TomasPavlovicPavlo/286_schematic/MCS3201_IBM_PC_XT_AT_Floppy_Disk_Controller_1991.pdf

This Material Copyrighted By Its Respective Manufacturer
