TomasPavlovicPavlo/286_schematic/P80C287-8.pdf

This Material Copyrighted By Its Respective Manufacturer

# www.datasheet.live
