TomasPavlovicPavlo/286_schematic/HM6818.pdf

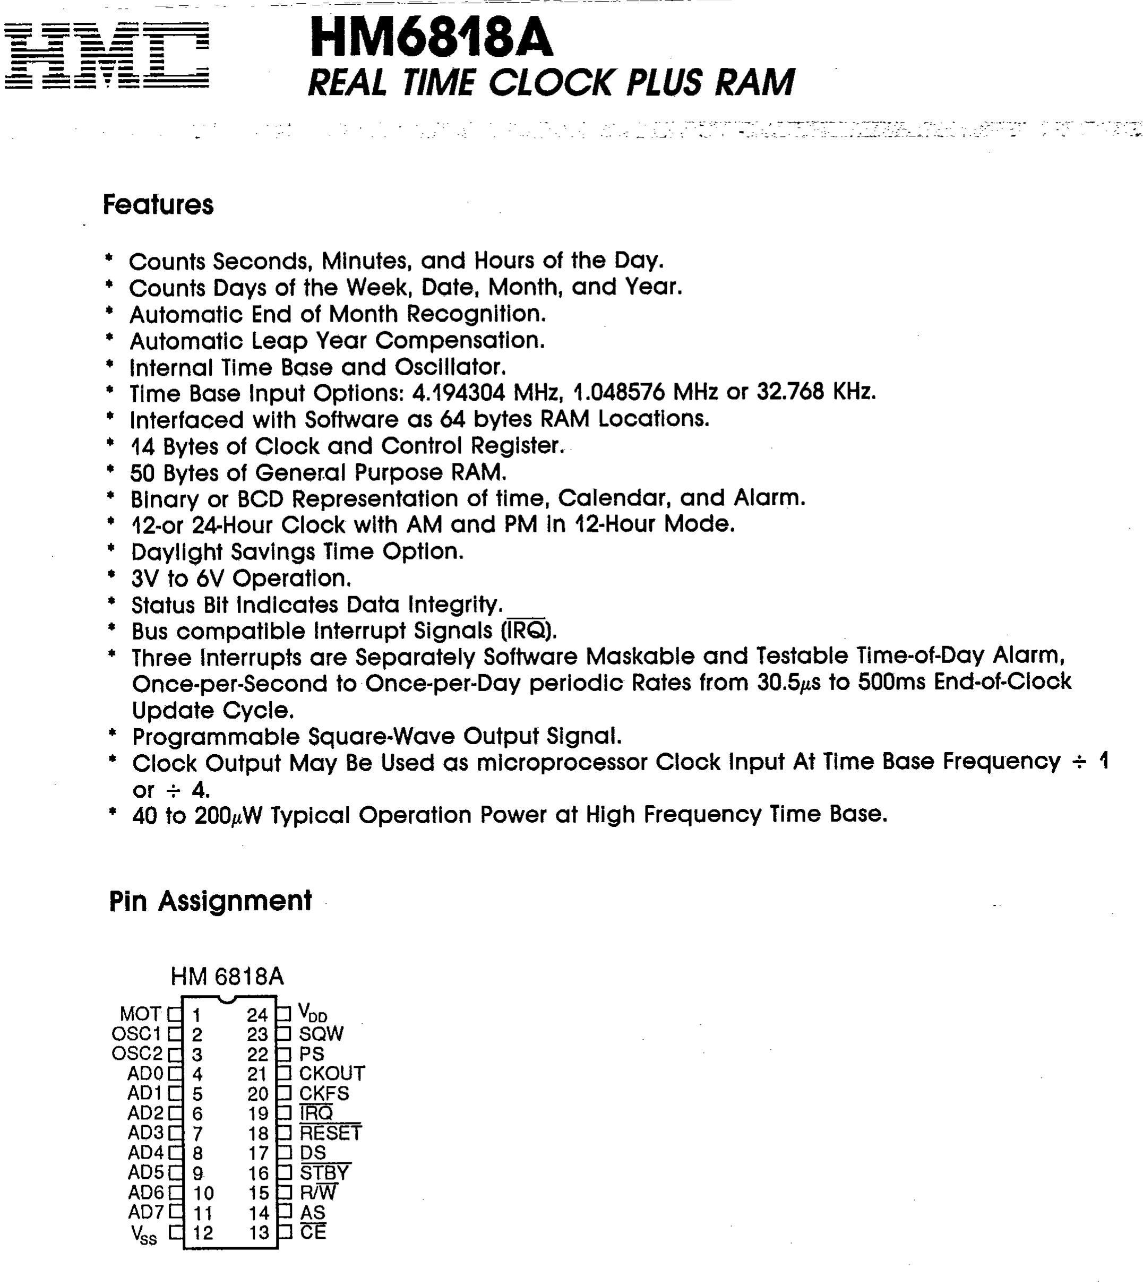
[picture p4: page 1]
