TomasPavlovicPavlo/286_schematic/IDE_controller/bot.jpg

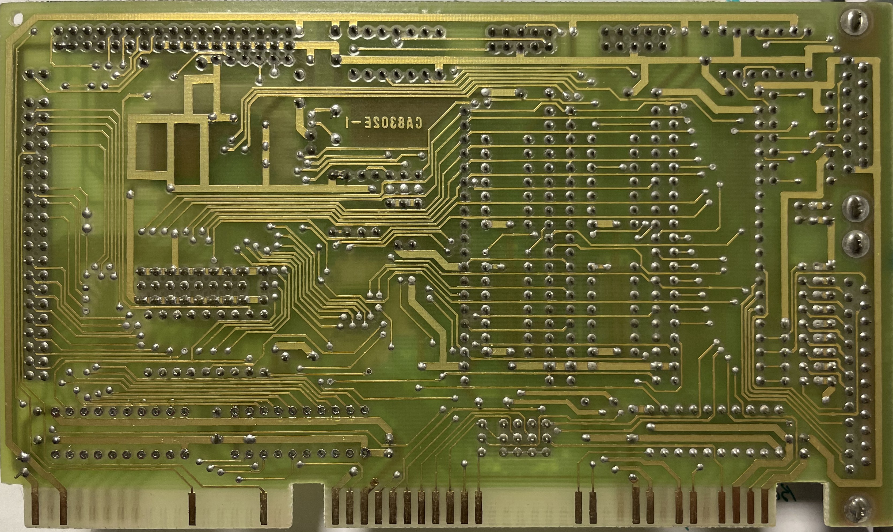
IDE_controller/bot.jpg
