TomasPavlovicPavlo/286_schematic/IDE_controller/IMG_6850.JPG

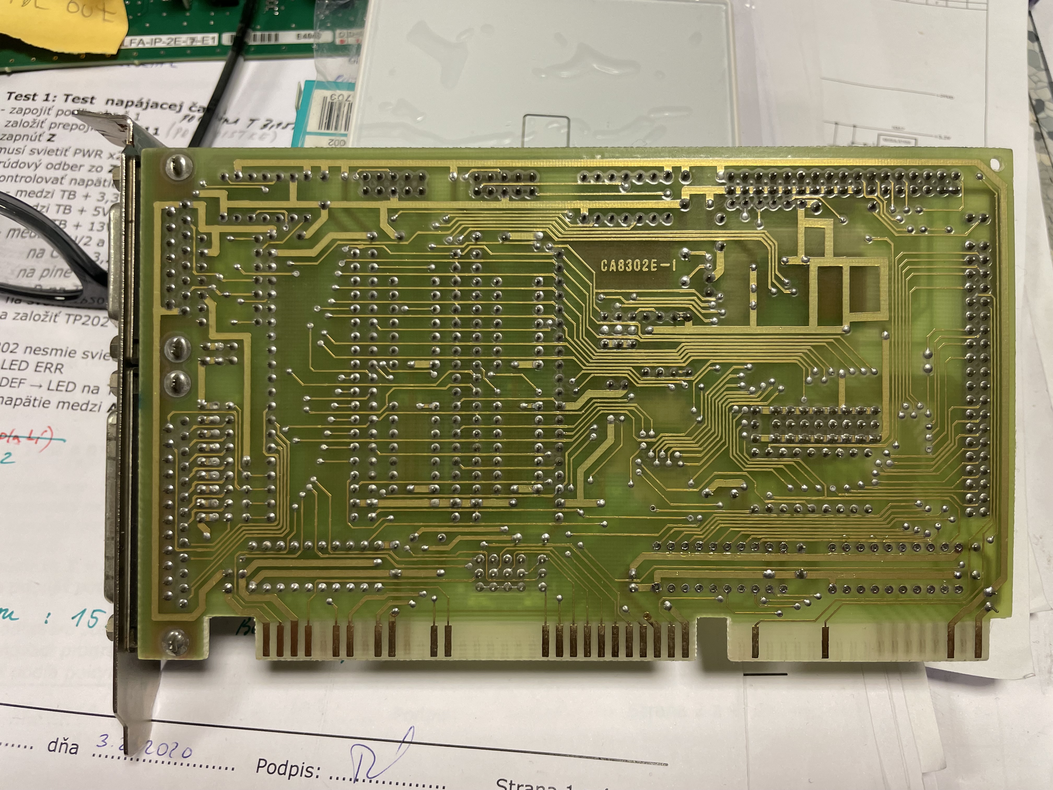
IDE_controller/IMG_6850.JPG
