TomasPavlovicPavlo/286_schematic/IDE_controller/IMG_6851.JPG

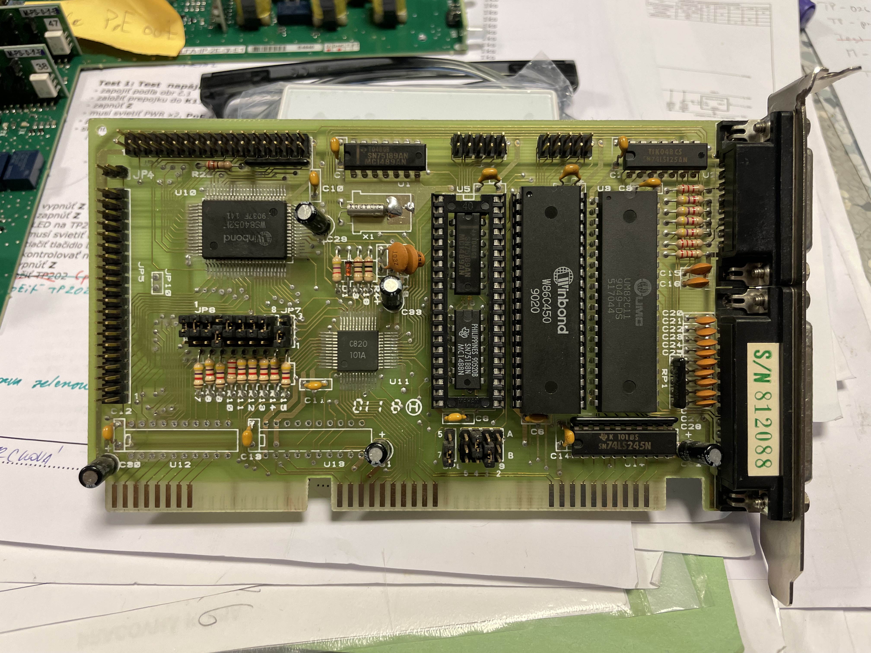
IDE_controller/IMG_6851.JPG
