TomasPavlovicPavlo/286_schematic/IDE_controller/top2.jpg

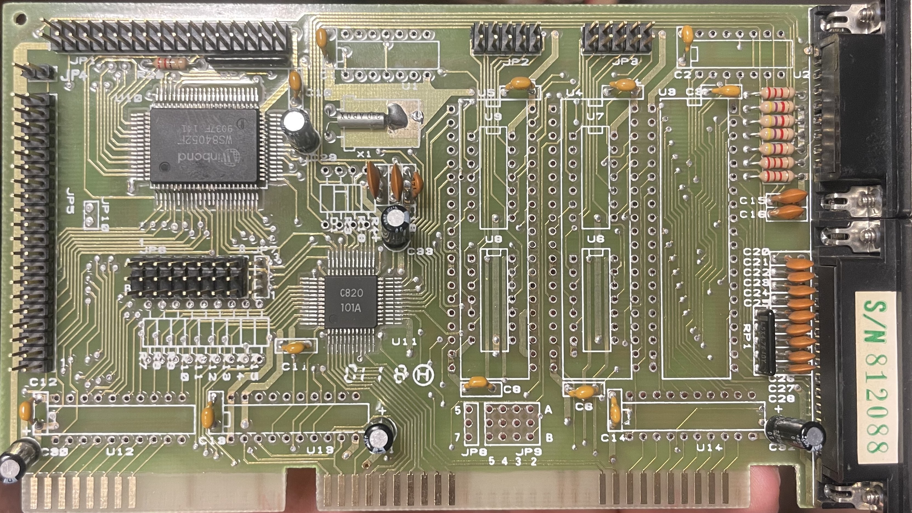
IDE_controller/top2.jpg
