TomasPavlovicPavlo/286_schematic/IDE_controller/top.jpg

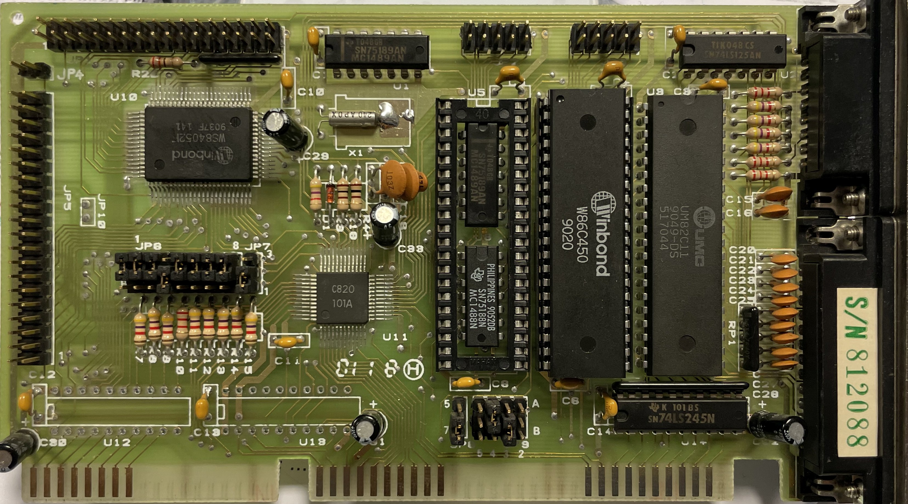
IDE_controller/top.jpg
