TomasPavlovicPavlo/286_schematic/KiCAD/suntac-286p-back-6633c3940dea2172361565.jpg

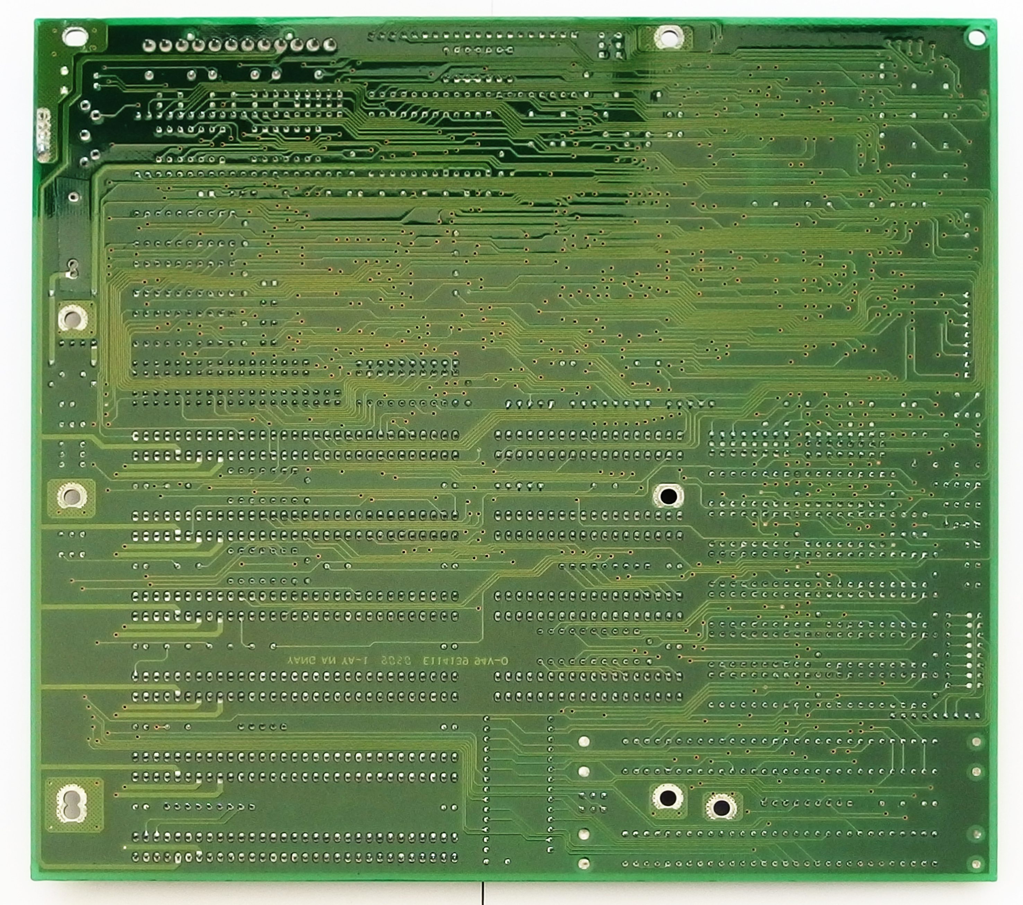
KiCAD/suntac-286p-back-6633c3940dea2172361565.jpg
