TomasPavlovicPavlo/286_schematic/KiCAD/top1.jpg

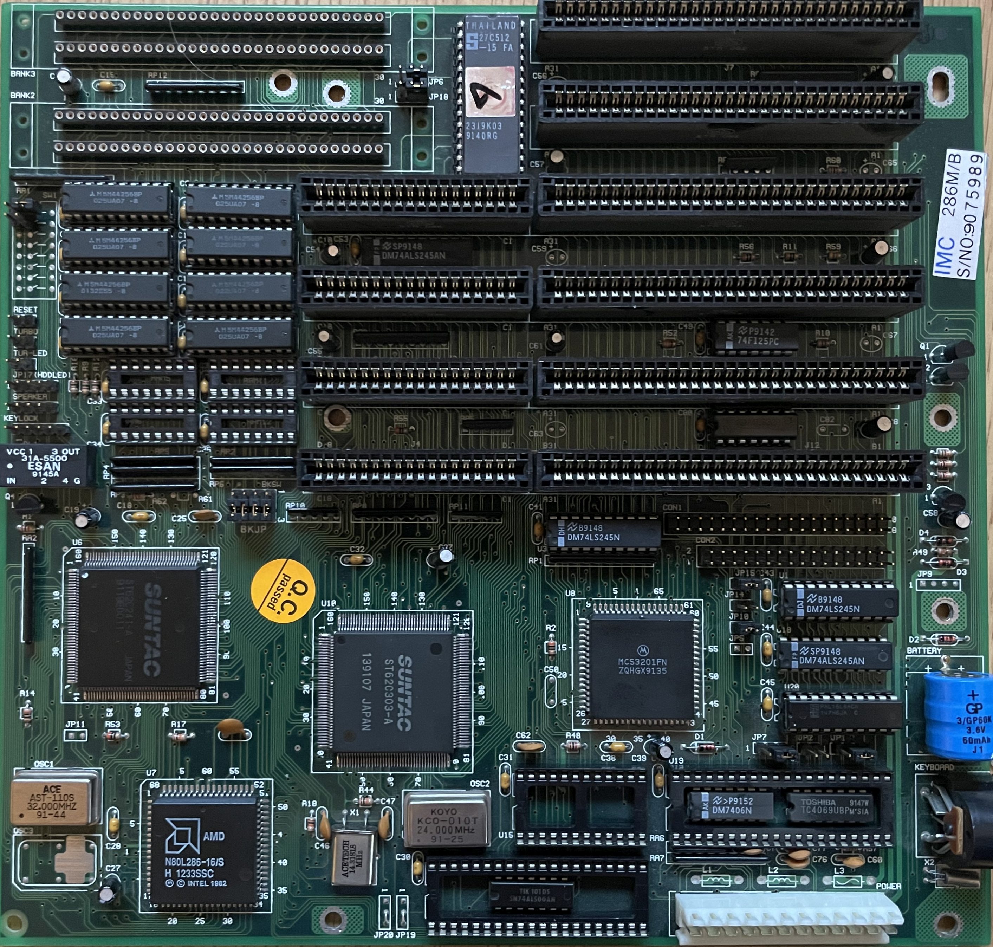
KiCAD/top1.jpg
