TomasPavlovicPavlo/286_schematic/KiCAD/top4.jpg

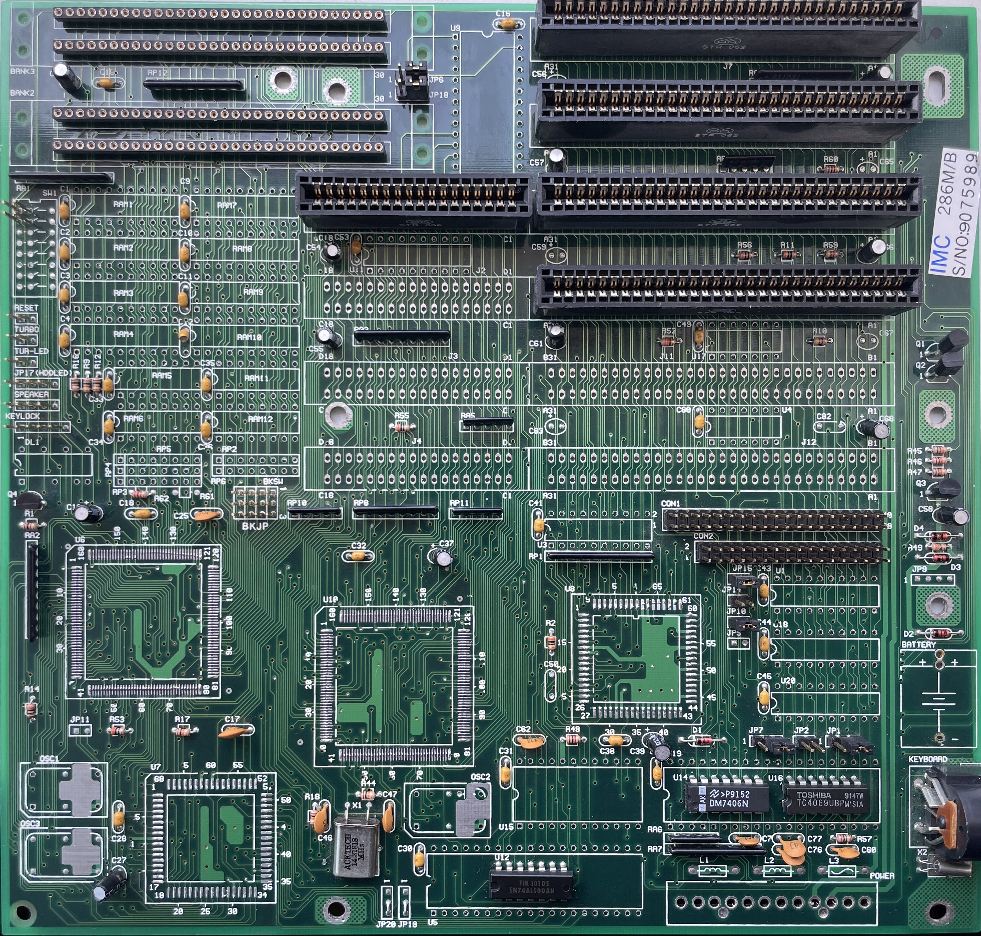
KiCAD/top4.jpg
