TomasPavlovicPavlo/286_schematic/KiCAD/top.jpg

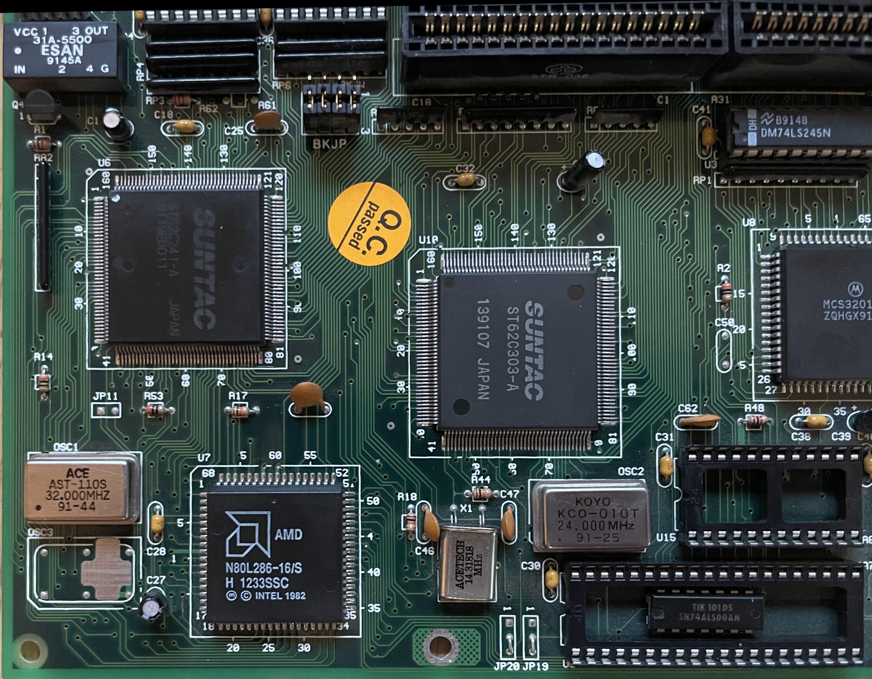
KiCAD/top.jpg
