TomasPavlovicPavlo/286_schematic/KiCAD/CPU_ChipSet1.kicad_sch

## KiCad design KiCAD/CPU_ChipSet1.kicad_sch (2025-07-21)

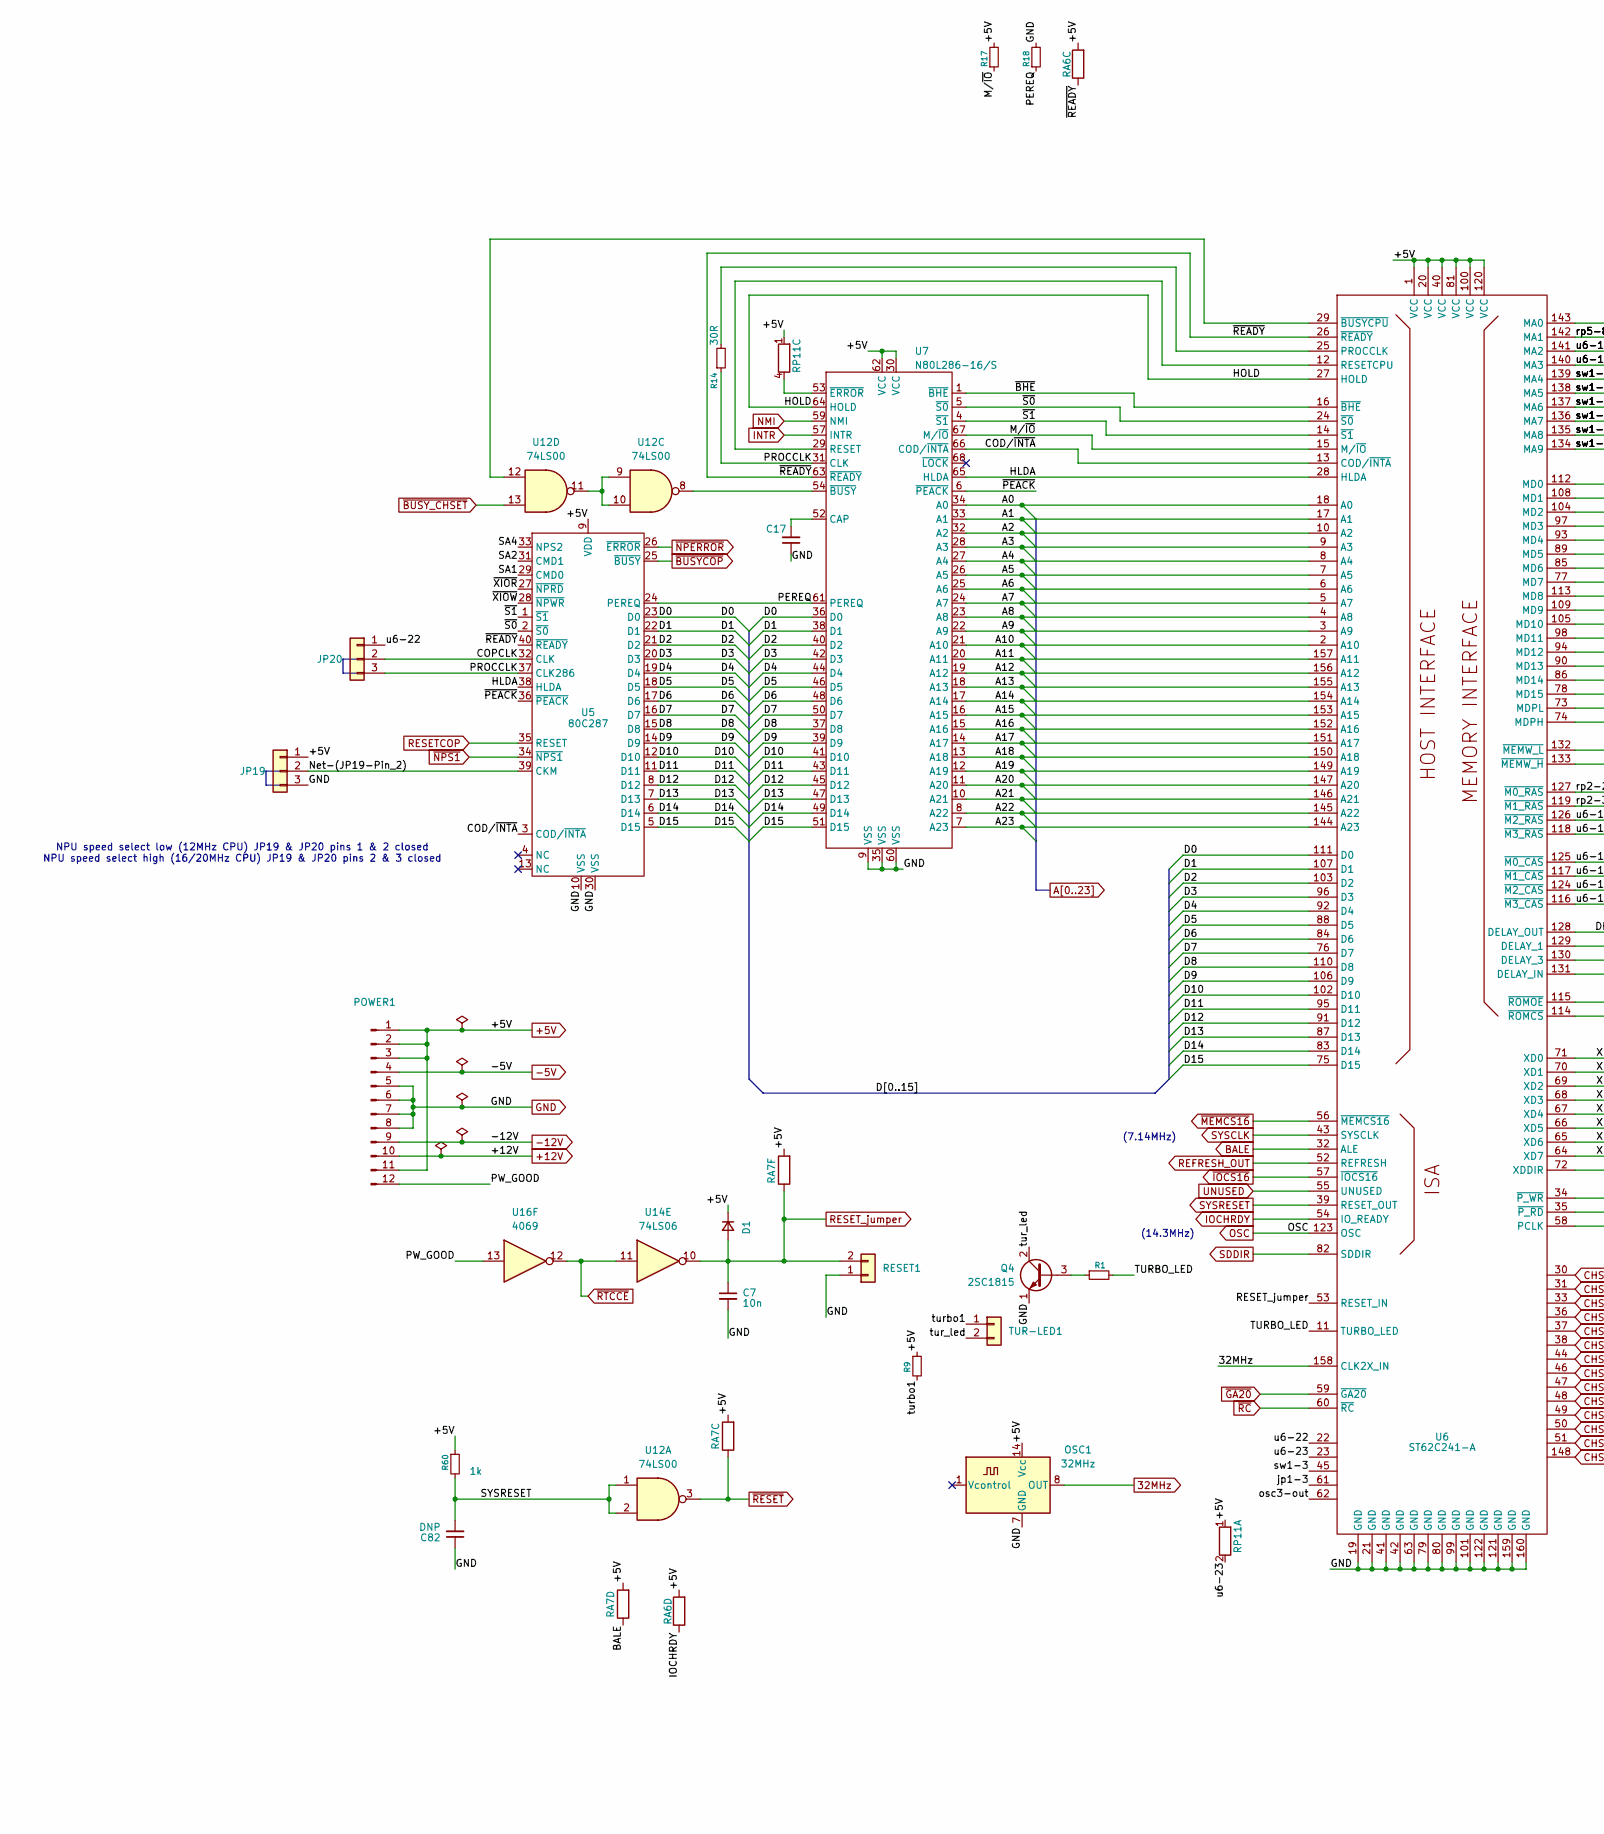
[picture p27: schematic CPU_ChipSet1.kicad_sch, part in row 1, column 1]

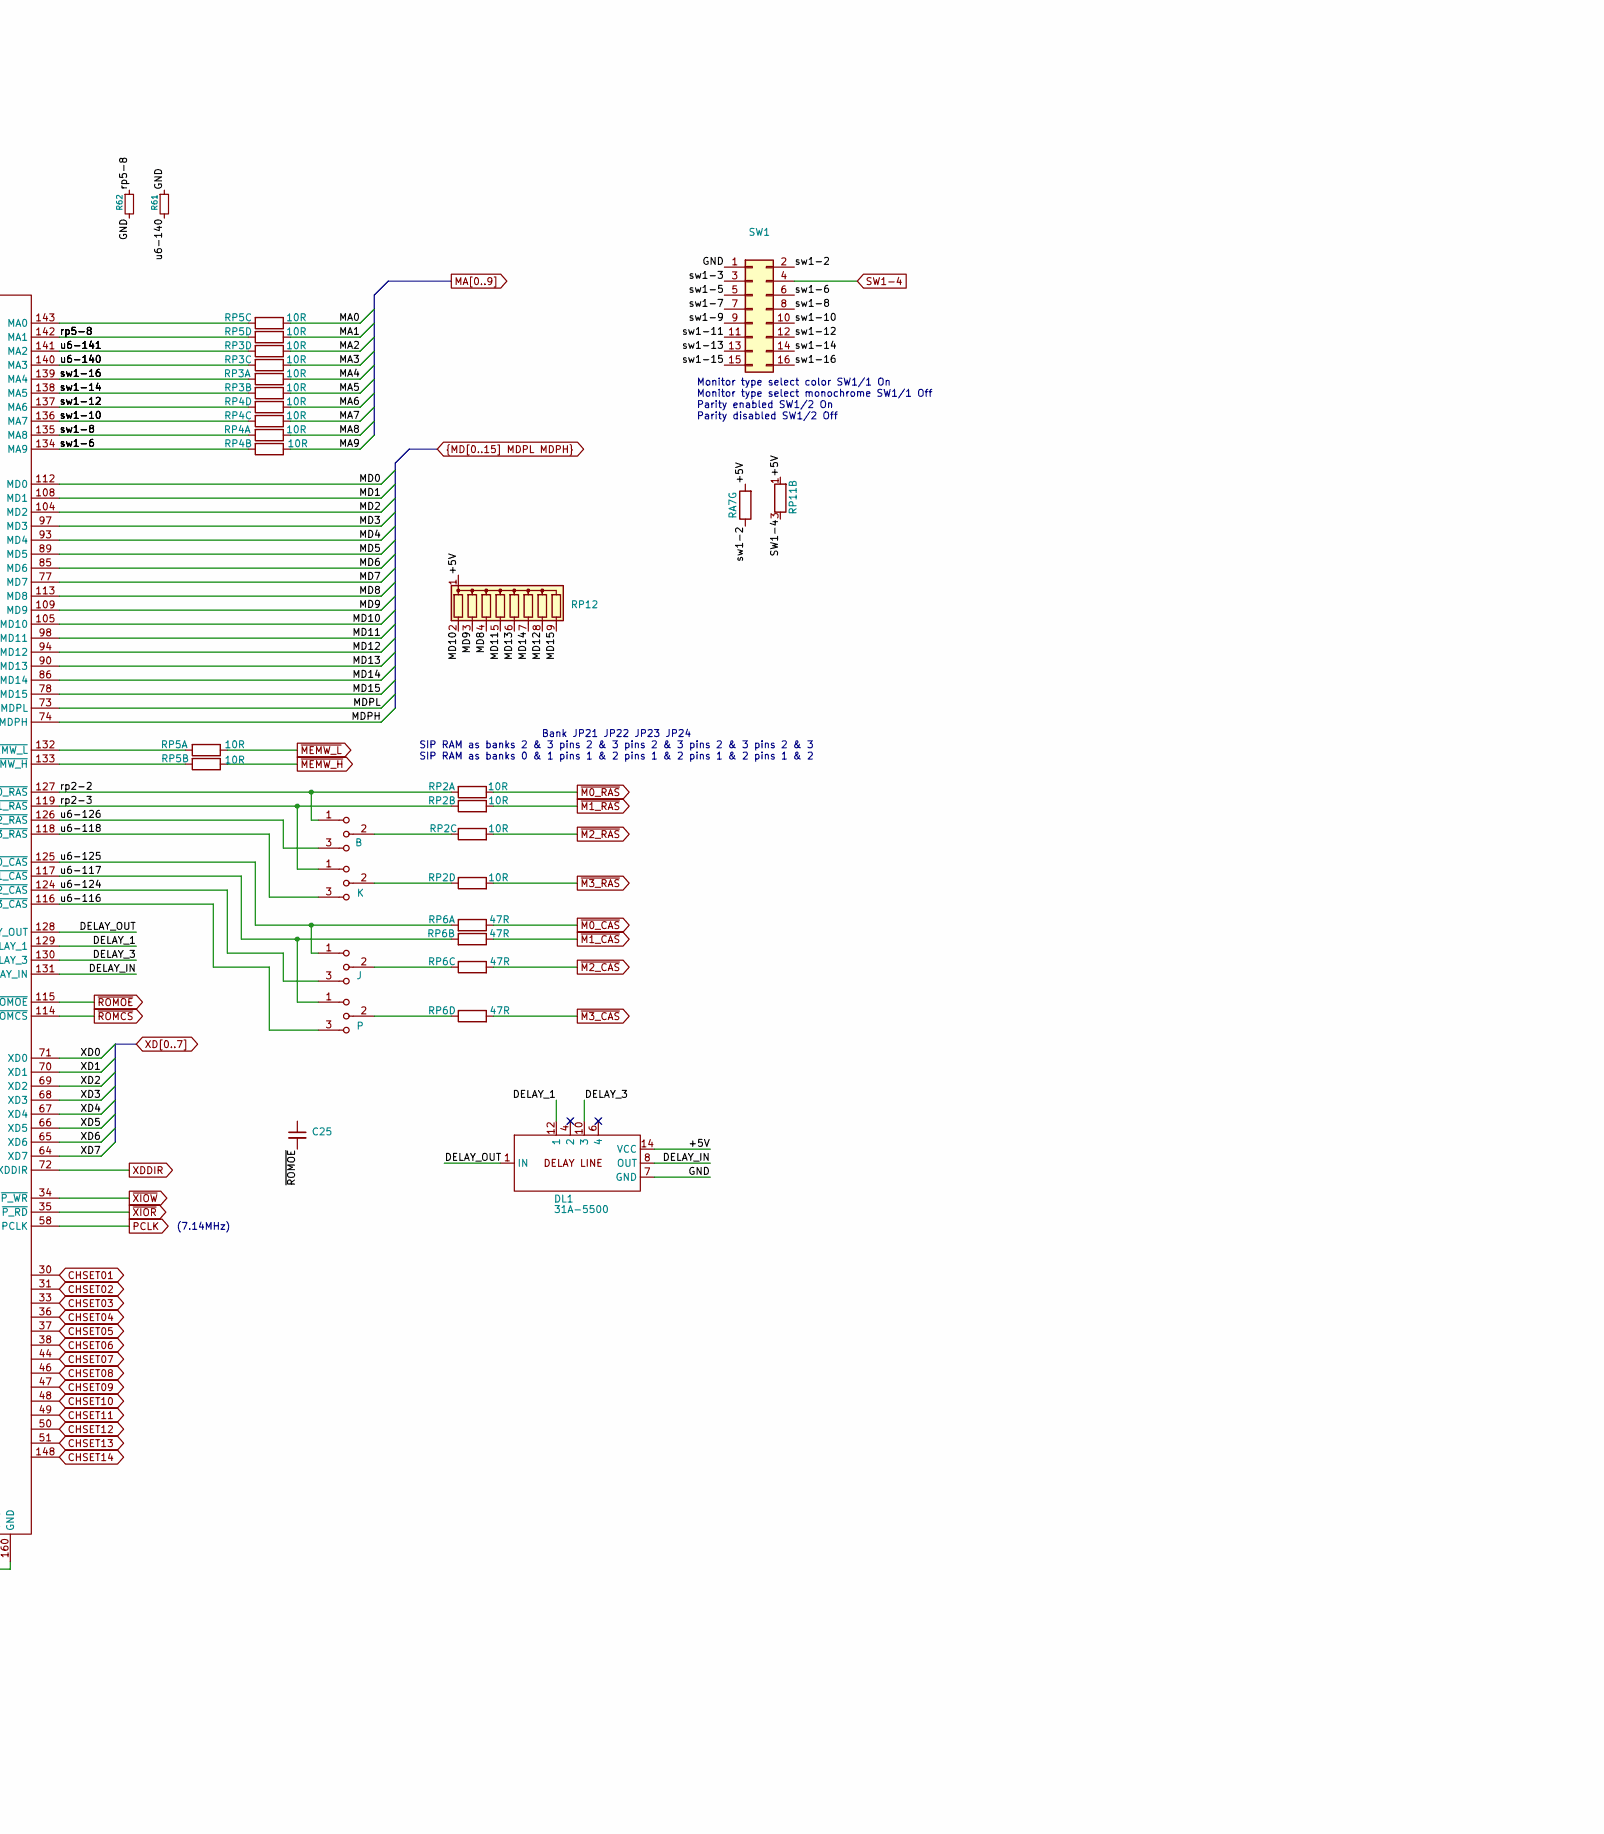
[picture p28: schematic CPU_ChipSet1.kicad_sch, part in row 1, column 2]

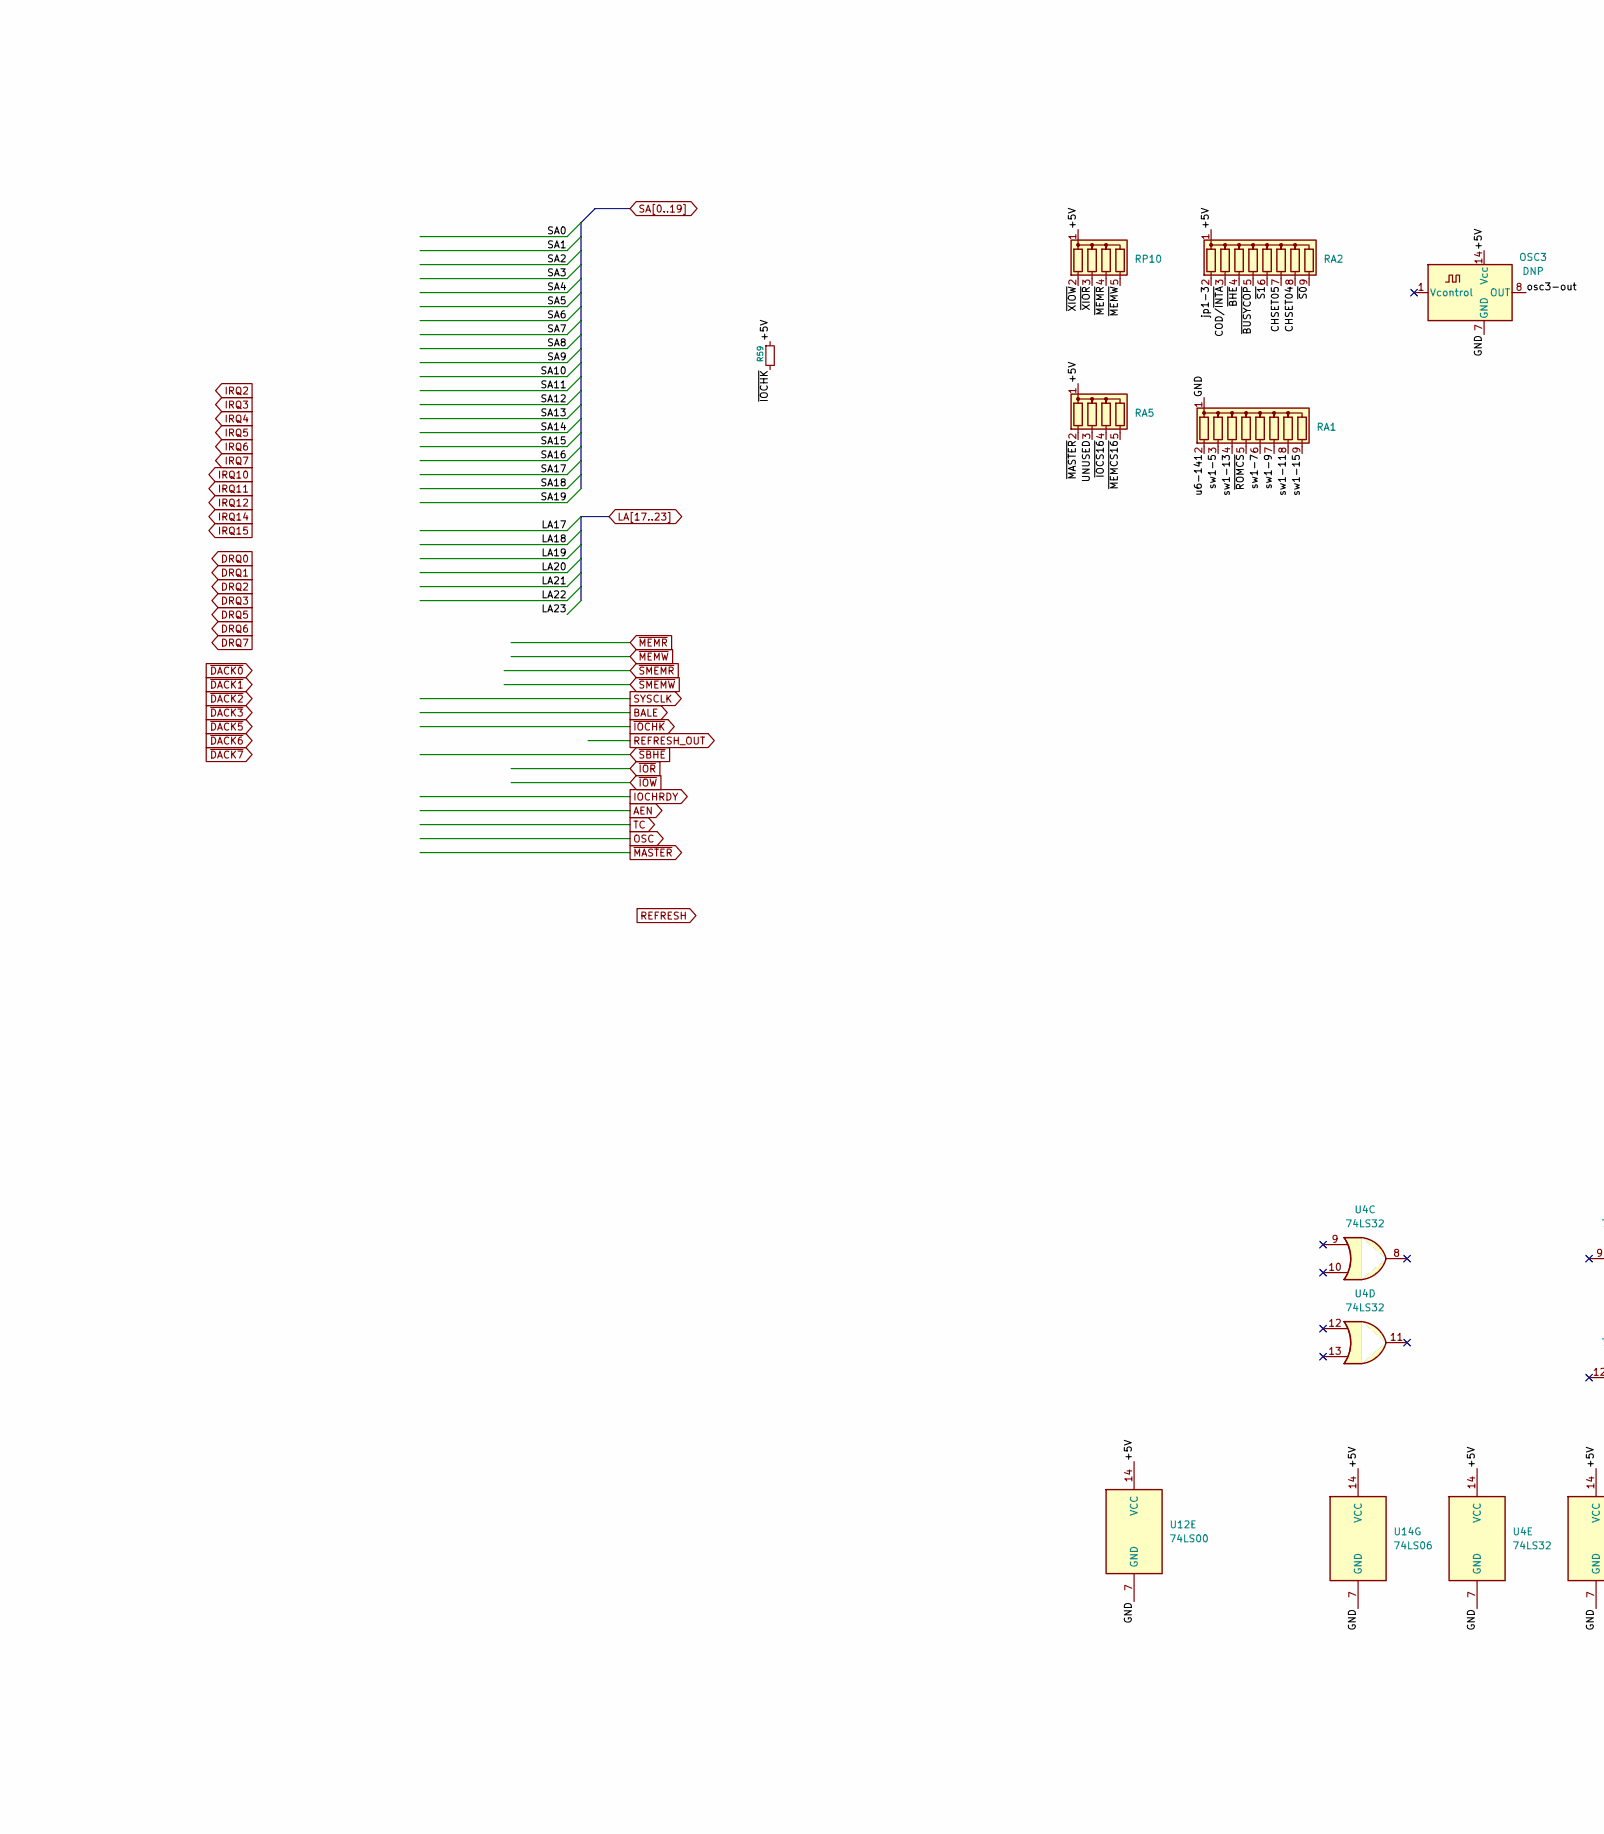
[picture p29: schematic CPU_ChipSet1.kicad_sch, part in row 2, column 1]

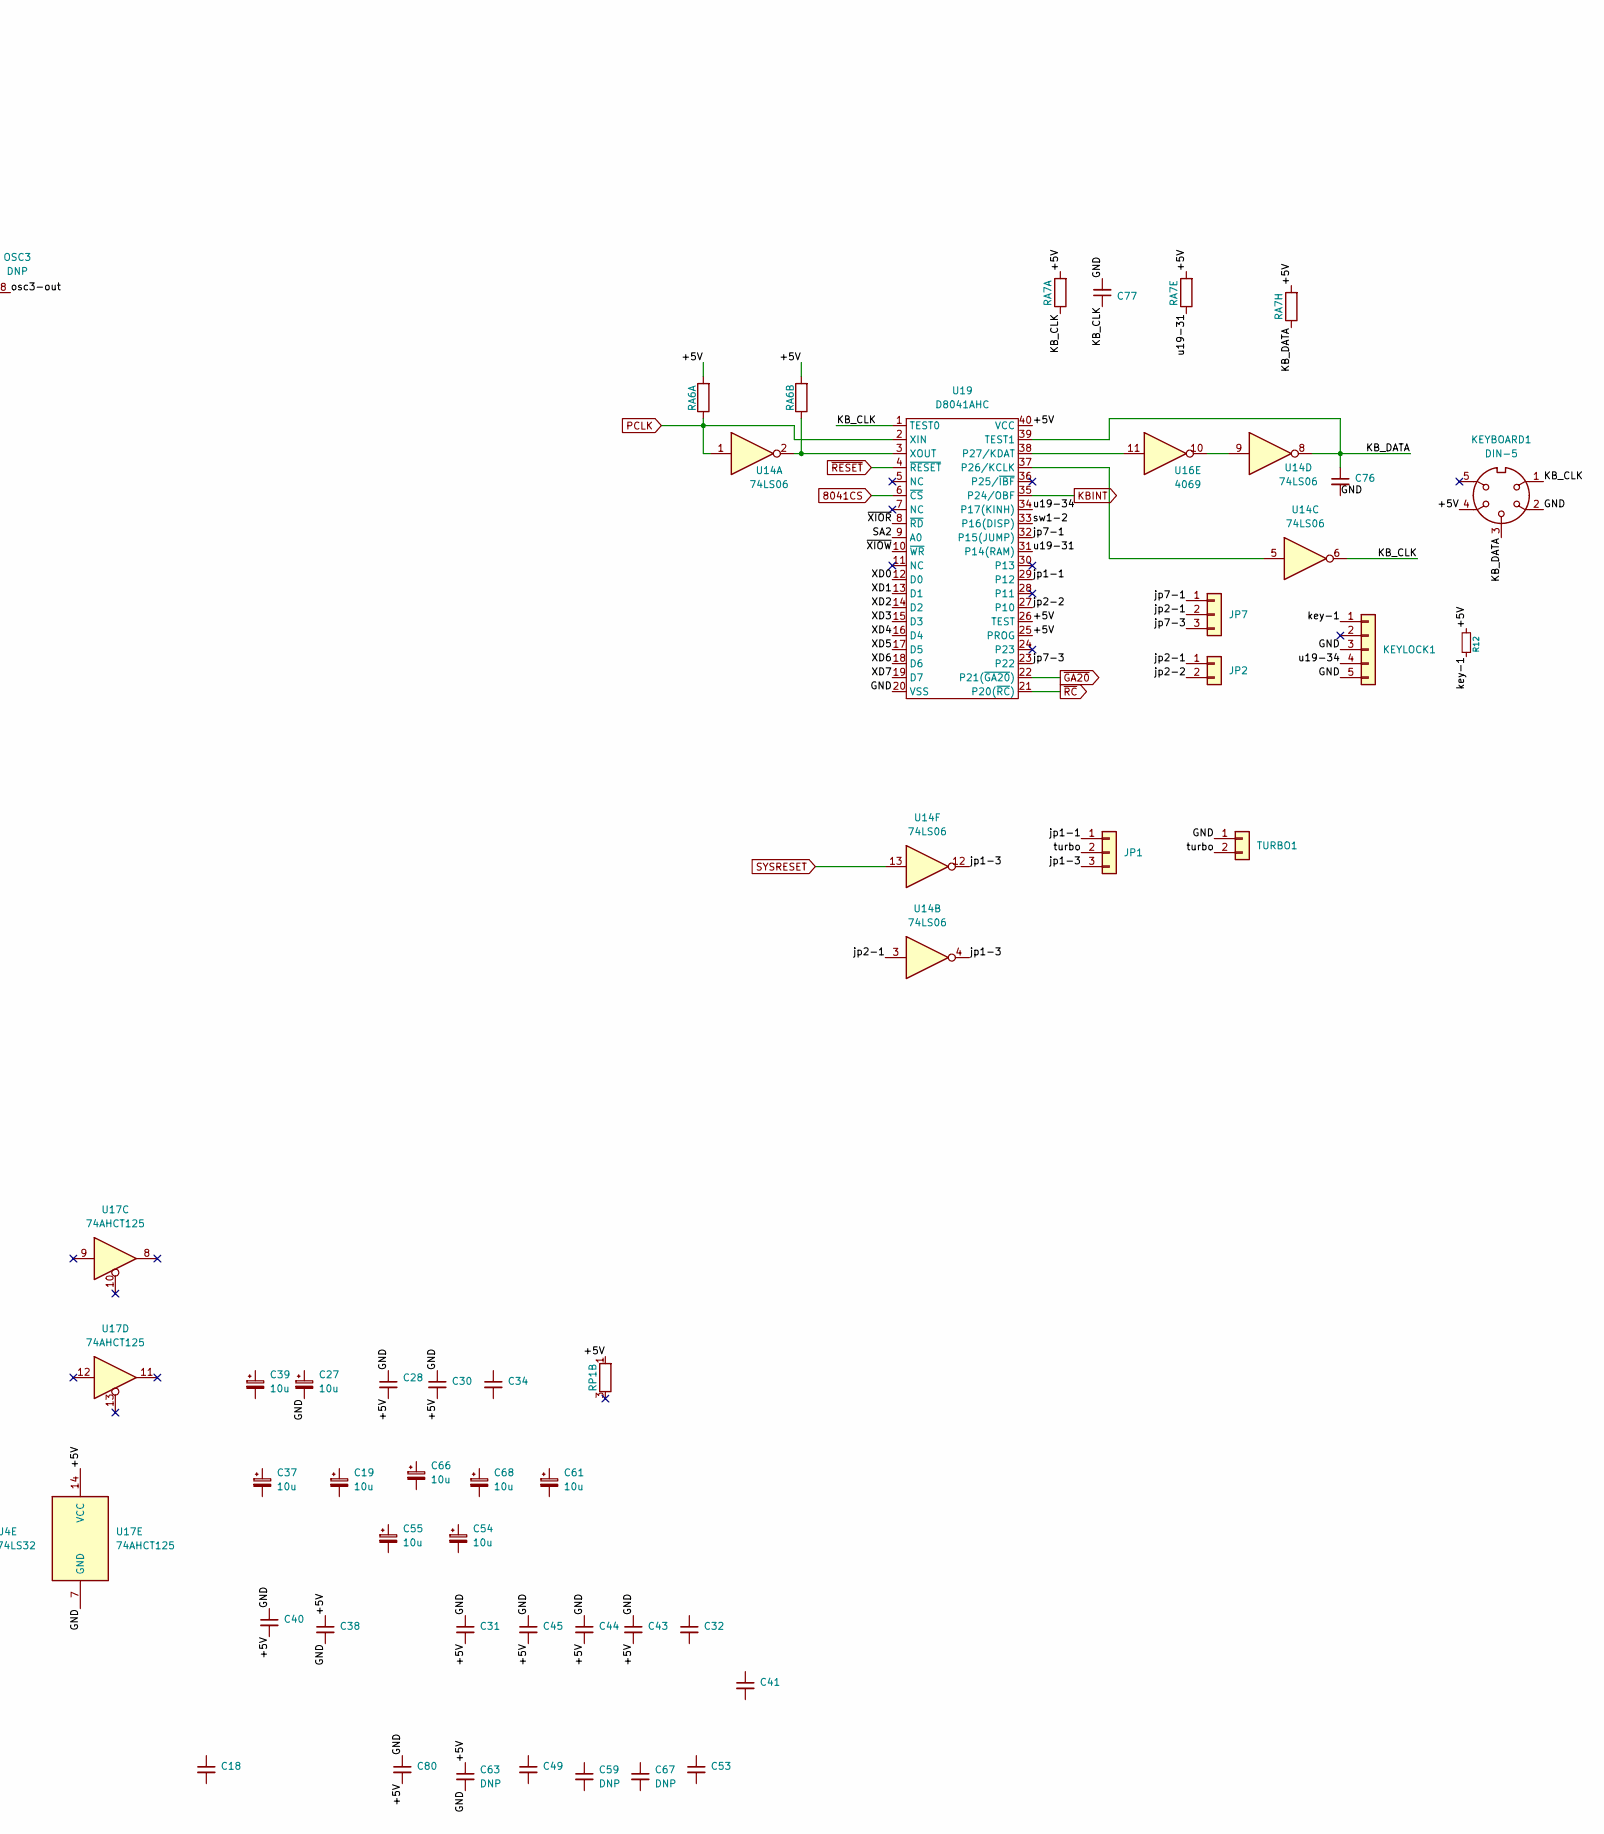
[picture p30: schematic CPU_ChipSet1.kicad_sch, part in row 2, column 2]

Parts:
BKSW1: B; PinHeader_1x03_P2.54mm_Vertical
BKSW2: K; PinHeader_1x03_P2.54mm_Vertical
BKSW3: J; PinHeader_1x03_P2.54mm_Vertical
BKSW4: P; PinHeader_1x03_P2.54mm_Vertical
C7: 10n; C_Disc_D4.3mm_W1.9mm_P5.00mm
C17, C18, C25, C28, C30, C31, C32, C34, C38, C40, C41, C43, C44, C45, C49, C53, C76, C77, C80: C_Disc_D4.3mm_W1.9mm_P5.00mm
C19, C27, C37, C39, C54, C55, C61, C66, C68: 10u; CP_Radial_D5.0mm_P2.50mm
C59, C63, C67: DNP; C_Disc_D3.0mm_W1.6mm_P2.50mm
C82: DNP; C_Disc_D4.3mm_W1.9mm_P5.00mm
D1: D_Small; D_A-405_P10.16mm_Horizontal
DL1: 31A-5500
JP1, JP7, JP19, JP20: Conn_01x03; PinHeader_1x03_P2.54mm_Vertical
JP2: Conn_01x02; PinSocket_1x02_P2.54mm_Vertical
KEYBOARD1: DIN-5; 286_DIN5
KEYLOCK1: Conn_01x05; PinHeader_1x05_P2.54mm_Vertical
OSC1: 32MHz; Oscillator_DIP-14
OSC3: DNP; Oscillator_DIP-14
POWER1: Conn_01x12_Pin; Molex_KK-396_A-41791-0012_1x12_P3.96mm_Vertical
Q4: 2SC1815; TO-92L_Inline_Wide
R1, R17, R18, R59, R61, R62: R_Small; R_Axial_DIN0204_L3.6mm_D1.6mm_P5.08mm_Horizontal
R9, R12: R_Small; R_Axial_L3.6mm_D1.6mm_P4.5mm_Horizontal
R14: 30R; R_Axial_DIN0204_L3.6mm_D1.6mm_P5.08mm_Horizontal
R60: 1k; R_Axial_L3.6mm_D1.6mm_P4.5mm_Horizontal
RA1, RA2, RA7: R_Network08; R_Array_SIP9
RA5, RA6: R_Network04; R_Array_SIP5
RESET1: Conn_01x02; PinSocket_1x02_P2.54mm_Vertical
RP1: R_Network09; R_Array_SIP10
RP2, RP3, RP4, RP5: 10R; R_Array_SIP8
RP6: 47R; R_Array_SIP8
RP10, RP11: R_Network04; R_Array_SIP5
RP12: R_Network08; R_Array_SIP9
SW1: Conn_02x08_Odd_Even; PinHeader_2x08_P2.54mm_Vertical
TUR-LED1: Conn_01x02; PinSocket_1x02_P2.54mm_Vertical
TURBO1: Conn_01x02; PinSocket_1x02_P2.54mm_Vertical
U4: 74LS32; DIP-14_W7.62mm
U5: 80C287; DIP-40_W15.24mm_Socket_small_pad
U6: ST62C241-A; PQFP-160_28x28mm_P0.65mm
U7: N80L286-16/S; PLCC-68_from_1
U12: 74LS00; DIP-14_W7.62mm
U14: 74LS06; DIP-14_W7.62mm
U16: 4069; DIP-14_W7.62mm
U17: 74AHCT125; DIP-14_W7.62mm
U19: D8041AHC; DIP-40_W15.24mm_Socket_small_pad

Connections:
32MHz: OSC1.8 (OUT), U6.158 (CLK2X_IN)
8041CS: U19.6 (~CS)
+5V: C28.2, C30.2, C31.2, C38.1, C40.2, C43.2, C44.2, C45.2, C63.1, C80.2, D1.1 (K), DL1.14 (VCC), JP19.1, KEYBOARD1.4, OSC1.14 (Vcc), OSC3.14 (Vcc), POWER1.1, POWER1.2, POWER1.3, POWER1.11, R9.1, R12.2, R17.2, R59.1, R60.1, RA2.1 (common), RA5.1 (common), RA6.1 (R1), RA7.1 (R1), RP1.1 (R1), RP10.1 (common), RP11.1 (R1), RP12.1 (common), U4.14 (VCC), U5.9 (VDD), U6.1 (VCC), U6.20 (VCC), U6.40 (VCC), U6.81 (VCC), U6.100 (VCC), U6.120 (VCC), U7.30 (VCC), U7.62 (VCC), U12.14 (VCC), U14.14 (VCC), U17.14 (VCC), U19.25 (PROG), U19.26 (TEST), U19.40 (VCC)
+12V: POWER1.10
-5V: POWER1.4
-12V: POWER1.9
A0: U6.18 (A0), U7.34 (A0)
A1: U6.17 (A1), U7.33 (A1)
A2: U6.10 (A2), U7.32 (A2)
A3: U6.9 (A3), U7.28 (A3)
A4: U6.8 (A4), U7.27 (A4)
A5: U6.7 (A5), U7.26 (A5)
A6: U6.6 (A6), U7.25 (A6)
A7: U6.5 (A7), U7.24 (A7)
A8: U6.4 (A8), U7.23 (A8)
A9: U6.3 (A9), U7.22 (A9)
A10: U6.2 (A10), U7.21 (A10)
A11: U6.157 (A11), U7.20 (A11)
A12: U6.156 (A12), U7.19 (A12)
A13: U6.155 (A13), U7.18 (A13)
A14: U6.154 (A14), U7.17 (A14)
A15: U6.153 (A15), U7.16 (A15)
A16: U6.152 (A16), U7.15 (A16)
A17: U6.151 (A17), U7.14 (A17)
A18: U6.150 (A18), U7.13 (A18)
A19: U6.149 (A19), U7.12 (A19)
A20: U6.147 (A20), U7.11 (A20)
A21: U6.146 (A21), U7.10 (A21)
A22: U6.145 (A22), U7.8 (A22)
A23: U6.144 (A23), U7.7 (A23)
BALE: RA7.5 (R4.2), U6.32 (ALE)
CHSET01: U6.30
CHSET02: U6.31
CHSET03: U6.33
CHSET04: RA2.8 (R7), U6.36
CHSET05: RA2.7 (R6), U6.37
CHSET06: U6.38
CHSET07: U6.44
CHSET08: U6.46
CHSET09: U6.47
CHSET10: U6.48
CHSET11: U6.49
CHSET12: U6.50
CHSET13: U6.51
CHSET14: U6.148
COD/~INTA: RA2.3 (R2), U5.3 (COD/~INTA), U6.13 (COD/~INTA), U7.66 (COD/~INTA)
COPCLK: JP20.2, U5.32 (CLK)
D0: U5.23 (D0), U6.111 (D0), U7.36 (D0)
D1: U5.22 (D1), U6.107 (D1), U7.38 (D1)
D2: U5.21 (D2), U6.103 (D2), U7.40 (D2)
D3: U5.20 (D3), U6.96 (D3), U7.42 (D3)
D4: U5.19 (D4), U6.92 (D4), U7.44 (D4)
D5: U5.18 (D5), U6.88 (D5), U7.46 (D5)
D6: U5.17 (D6), U6.84 (D6), U7.48 (D6)
D7: U5.16 (D7), U6.76 (D7), U7.50 (D7)
D8: U5.15 (D8), U6.110 (D8), U7.37 (D8)
D9: U5.14 (D9), U6.106 (D9), U7.39 (D9)
D10: U5.12 (D10), U6.102 (D10), U7.41 (D10)
D11: U5.11 (D11), U6.95 (D11), U7.43 (D11)
D12: U5.8 (D12), U6.91 (D12), U7.45 (D12)
D13: U5.7 (D13), U6.87 (D13), U7.47 (D13)
D14: U5.6 (D14), U6.83 (D14), U7.49 (D14)
D15: U5.5 (D15), U6.75 (D15), U7.3 (NC), U7.51 (D15), U7.56 (NC)
DELAY_1: DL1.12 (1), U6.129 (DELAY_1)
DELAY_3: DL1.10 (3), U6.130 (DELAY_3)
DELAY_IN: DL1.8 (OUT), U6.131 (DELAY_IN)
DELAY_OUT: DL1.1 (IN), U6.128 (DELAY_OUT)
GND: C7.2, C17.1, C27.2, C28.1, C30.1, C31.1, C38.2, C40.1, C43.1, C44.1, C45.1, C63.2, C76.2, C77.2, C80.1, C82.1, DL1.7 (GND), JP19.3, KEYBOARD1.2, KEYLOCK1.3, KEYLOCK1.5, OSC1.7 (GND), OSC3.7 (GND), POWER1.5, POWER1.6, POWER1.7, POWER1.8, Q4.1 (E), R18.2, R61.1, R62.2, RA1.1 (common), RESET1.1, SW1.1, TURBO1.1, U4.7 (GND), U5.10 (VSS), U5.30 (VSS), U6.19 (GND), U6.21 (GND), U6.41 (GND), U6.42 (GND), U6.63 (GND), U6.79 (GND), U6.80 (GND), U6.99 (GND), U6.101 (GND), U6.121 (GND), U6.122 (GND), U6.159 (GND), U6.160 (GND), U7.9 (VSS), U7.35 (VSS), U7.60 (VSS), U12.7 (GND), U14.7 (GND), U17.7 (GND), U19.20 (VSS)
HLDA: U5.38 (HLDA), U6.28 (HLDA), U7.65 (HLDA)
HOLD: U6.27 (HOLD), U7.64 (HOLD)
INTR: U7.57 (INTR)
IOCHRDY: RA6.5 (R4.2), U6.54 (IO_READY)
KBINT: U19.35 (P24/OBF)
KB_CLK: C77.1, KEYBOARD1.1, RA7.2 (R1.2), U14.6, U19.1 (TEST0)
KB_DATA: C76.1, KEYBOARD1.3, RA7.9 (R8.2), U14.8, U19.39 (TEST1)
MA0: RP5.5 (R3.1)
MA1: RP5.7 (R4.1)
MA2: RP3.7 (R4.1)
MA3: RP3.5 (R3.1)
MA4: RP3.1 (R1.1)
MA5: RP3.3 (R2.1)
MA6: RP4.7 (R4.1)
MA7: RP4.5 (R3.1)
MA8: RP4.1 (R1.1)
MA9: RP4.3 (R2.1)
MD0: U6.112 (MD0)
MD1: U6.108 (MD1)
MD2: U6.104 (MD2)
MD3: U6.97 (MD3)
MD4: U6.93 (MD4)
MD5: U6.89 (MD5)
MD6: U6.85 (MD6)
MD7: U6.77 (MD7)
MD8: RP12.4 (R3), U6.113 (MD8)
MD9: RP12.3 (R2), U6.109 (MD9)
MD10: RP12.2 (R1), U6.105 (MD10)
MD11: RP12.5 (R4), U6.98 (MD11)
MD12: RP12.8 (R7), U6.94 (MD12)
MD13: RP12.6 (R5), U6.90 (MD13)
MD14: RP12.7 (R6), U6.86 (MD14)
MD15: RP12.9 (R8), U6.78 (MD15)
MDPH: U6.74 (MDPH)
MDPL: U6.73 (MDPL)
M/~IO: R17.1, U6.15 (M/~IO), U7.67 (M/~IO)
NMI: U7.59 (NMI)
unnamed: BKSW1.2, RP2.5 (R3.1)
unnamed: BKSW2.2, RP2.7 (R4.1)
unnamed: BKSW3.2, RP6.5 (R3.1)
unnamed: BKSW4.2, RP6.7 (R4.1)
unnamed: C17.2, U7.52 (CAP)
unnamed: JP19.2, U5.39 (CKM)
unnamed: Q4.3 (B), R1.1
unnamed: R14.2, U6.25 (PROCCLK)
unnamed: RA6.3 (R2.2), U14.2, U19.3 (XOUT)
unnamed: RP5.2 (R1.2), U6.132 (~MEMW_L)
unnamed: RP5.4 (R2.2), U6.133 (~MEMW_H)
unnamed: RP5.6 (R3.2), U6.143 (MA0)
unnamed: RP11.4 (R3.2), U7.53 (~ERROR)
unnamed: U6.12 (RESETCPU), U7.29 (RESET)
unnamed: U7.54 (~BUSY), U12.8
unnamed: U12.9, U12.10, U12.11
unnamed: U6.29 (~BUSYCPU), U12.12
unnamed: U14.5, U19.37 (P26/KCLK)
unnamed: U14.9, U16.10
unnamed: U16.11, U19.38 (P27/KDAT)
OSC: U6.123 (OSC)
PCLK: RA6.2 (R1.2), U6.58 (PCLK), U14.1, U19.2 (XIN)
PEREQ: R18.1, U5.24 (PEREQ), U7.61 (PEREQ)
PROCCLK: JP20.3, R14.1, U5.37 (CLK286), U7.31 (CLK)
PW_GOOD: POWER1.12, U16.13
REFRESH_OUT: U6.52 (REFRESH)
RESETCOP: U5.35 (RESET)
RESET_jumper: C7.1, D1.2 (A), RA7.7 (R6.2), RESET1.2, U6.53 (RESET_IN), U14.10
SA1: U5.29 (CMD0)
SA2: U5.31 (CMD1), U19.9 (A0)
SA4: U5.33 (NPS2)
SDDIR: U6.82 (SDDIR)
SW1-4: RP11.3 (R2.2), SW1.4
SYSCLK: U6.43 (SYSCLK)
SYSRESET: C82.2, R60.2, U6.39 (RESET_OUT), U12.1, U12.2, U14.13
TURBO_LED: R1.2, U6.11 (TURBO_LED)
UNUSED: RA5.3 (R2), U6.55 (UNUSED)
XD0: U6.71 (XD0), U19.12 (D0)
XD1: U6.70 (XD1), U19.13 (D1)
XD2: U6.69 (XD2), U19.14 (D2)
XD3: U6.68 (XD3), U19.15 (D3)
XD4: U6.67 (XD4), U19.16 (D4)
XD5: U6.66 (XD5), U19.17 (D5)
XD6: U6.65 (XD6), U19.18 (D6)
XD7: U6.64 (XD7), U19.19 (D7)
XDDIR: U6.72 (XDDIR)
jp1-1: JP1.1, U19.29 (P12)
jp1-3: JP1.3, RA2.2 (R1), U6.61, U14.4, U14.12
jp2-1: JP2.1, JP7.2, U14.3
jp2-2: JP2.2, U19.27 (P10)
jp7-1: JP7.1, U19.32 (P15(JUMP))
jp7-3: JP7.3, U19.23 (P22)
key-1: KEYLOCK1.1, R12.1
osc3-out: OSC3.8 (OUT), U6.62
rp2-2: BKSW1.1, RP2.2 (R1.2), U6.127 (~M0_RAS)
rp2-3: BKSW2.1, RP2.3 (R2.1), U6.119 (~M1_RAS)
rp5-8: R62.1, RP5.8 (R4.2), U6.142 (MA1)
sw1-2: RA7.8 (R7.2), SW1.2, U19.33 (P16(DISP))
sw1-3: SW1.3, U6.45
sw1-5: RA1.3 (R2), SW1.5
sw1-6: RP4.4 (R2.2), SW1.6, U6.134 (MA9)
sw1-7: RA1.6 (R5), SW1.7
sw1-8: RP4.2 (R1.2), SW1.8, U6.135 (MA8)
sw1-9: RA1.7 (R6), SW1.9
sw1-10: RP4.6 (R3.2), SW1.10, U6.136 (MA7)
sw1-11: RA1.8 (R7), SW1.11
sw1-12: RP4.8 (R4.2), SW1.12, U6.137 (MA6)
sw1-13: RA1.4 (R3), SW1.13
sw1-14: RP3.4 (R2.2), SW1.14, U6.138 (MA5)
sw1-15: RA1.9 (R8), SW1.15
sw1-16: RP3.2 (R1.2), SW1.16, U6.139 (MA4)
tur_led: Q4.2 (C), TUR-LED1.2
turbo: JP1.2, TURBO1.2
turbo1: R9.2, TUR-LED1.1
u6-22: JP20.1, U6.22
u6-23: RP11.2 (R1.2), U6.23
u6-116: BKSW4.3, U6.116 (~M3_CAS)
u6-117: BKSW4.1, RP6.4 (R2.2), U6.117 (~M1_CAS)
u6-118: BKSW2.3, U6.118 (~M3_RAS)
u6-124: BKSW3.3, U6.124 (~M2_CAS)
u6-125: BKSW3.1, RP6.2 (R1.2), U6.125 (~M0_CAS)
u6-126: BKSW1.3, U6.126 (~M2_RAS)
u6-140: R61.2, RP3.6 (R3.2), U6.140 (MA3)
u6-141: RA1.2 (R1), RP3.8 (R4.2), U6.141 (MA2)
u19-31: RA7.6 (R5.2), U19.31 (P14(RAM))
u19-34: KEYLOCK1.4, U19.34 (P17(KINH))
~BHE: RA2.4 (R3), U6.16 (~BHE), U7.1 (~BHE)
~BUSYCOP: RA2.5 (R4), U5.25 (~BUSY)
~BUSY_CHSET: U12.13
~GA20: U6.59 (~GA20), U19.22 (P21(~GA20))
~IOCHK: R59.2
~IOCS16: RA5.4 (R3), U6.57 (~IOCS16)
~M0_CAS: RP6.1 (R1.1)
~M0_RAS: RP2.1 (R1.1)
~M1_CAS: RP6.3 (R2.1)
~M1_RAS: RP2.4 (R2.2)
~M2_CAS: RP6.6 (R3.2)
~M2_RAS: RP2.6 (R3.2)
~M3_CAS: RP6.8 (R4.2)
~M3_RAS: RP2.8 (R4.2)
~MASTER: RA5.2 (R1)
~MEMCS16: RA5.5 (R4), U6.56 (~MEMCS16)
~MEMR: RP10.4 (R3)
~MEMW_H: RP5.3 (R2.1)
~MEMW_L: RP5.1 (R1.1)
~MEMW: RP10.5 (R4)
~NPERROR: U5.26 (~ERROR)
~NPS1: U5.34 (~NPS1)
~PEACK: U5.36 (~PEACK), U7.6 (~PEACK)
~RC: U6.60 (~RC), U19.21 (P20(~RC))
~READY: RA6.4 (R3.2), U5.40 (~READY), U6.26 (~READY), U7.63 (~READY)
~RESET: RA7.4 (R3.2), U12.3, U19.4 (~RESET)
~ROMCS: RA1.5 (R4), U6.114 (~ROMCS)
~ROMOE: C25.2, U6.115 (~ROMOE)
~RTCCE: U14.11, U16.12
~S0: RA2.9 (R8), U5.2 (~S0), U6.24 (~S0), U7.5 (~S0)
~S1: RA2.6 (R5), U5.1 (~S1), U6.14 (~S1), U7.4 (~S1)
~XIOR: RP10.3 (R2), U5.27 (~NPRD), U6.35 (~P_RD), U19.8 (~RD)
~XIOW: RP10.2 (R1), U5.28 (~NPWR), U6.34 (~P_WR), U19.10 (~WR)

Notes on the sheet:
Bank JP21 JP22 JP23 JP24 SIP RAM as banks 2 & 3 pins 2 & 3 pins 2 & 3 pins 2 & 3 pins 2 & 3 SIP RAM as banks 0 & 1 pins 1 & 2 pins 1 & 2 pins 1 & 2 pins 1 & 2
(7.14MHz)
NPU speed select low (12MHz CPU) JP19 & JP20 pins 1 & 2 closed NPU speed select high (16/20MHz CPU) JP19 & JP20 pins 2 & 3 closed
(14.3MHz)
Monitor type select color SW1/1 On Monitor type select monochrome SW1/1 Off Parity enabled SW1/2 On Parity disabled SW1/2 Off
