TomasPavlovicPavlo/286_schematic/KiCAD/ChipSet2.kicad_sch

## KiCad design KiCAD/ChipSet2.kicad_sch (2025-07-21)

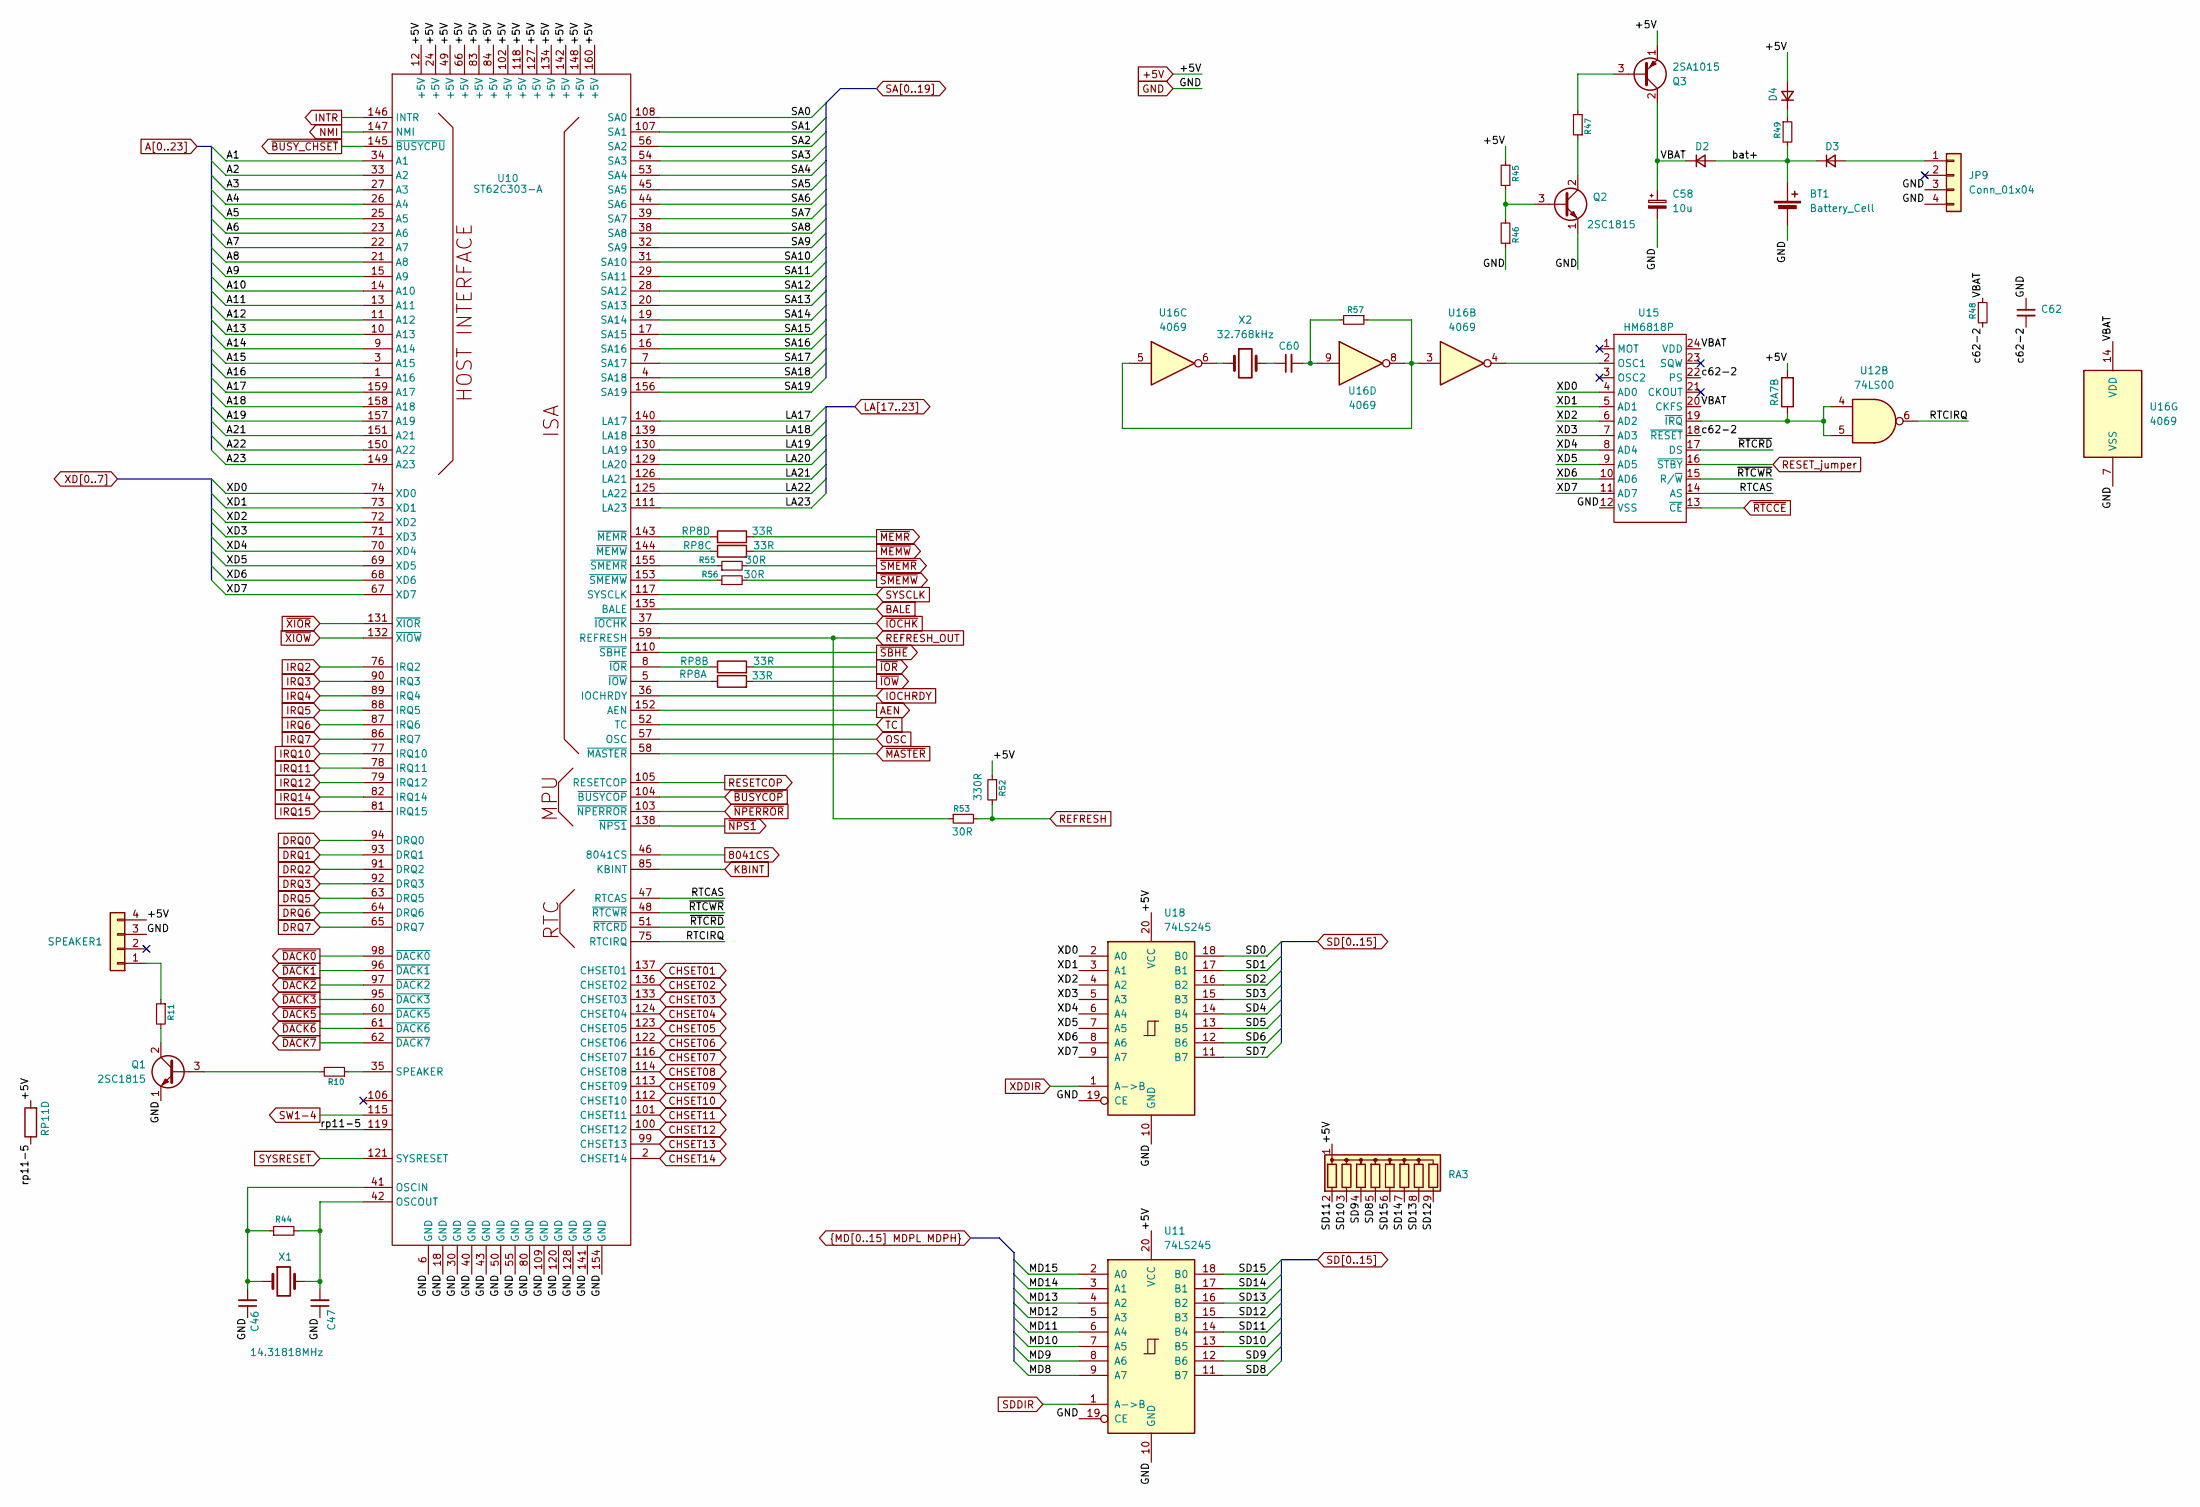
[picture p31: schematic ChipSet2.kicad_sch]

Parts:
BT1: Battery_Cell; 286_bat
C46, C47, C60, C62: C_Disc_D4.3mm_W1.9mm_P5.00mm
C58: 10u; CP_Radial_D5.0mm_P2.50mm
D2, D3, D4: D_Small; D_A-405_P10.16mm_Horizontal
JP9: Conn_01x04; PinHeader_1x04_P2.54mm_Vertical
Q1, Q2: 2SC1815; TO-92L_Inline_Wide
Q3: 2SA1015; TO-92L_Inline_Wide
R10, R11, R45, R46, R47, R49: R_Small; R_Axial_DIN0204_L3.6mm_D1.6mm_P5.08mm_Horizontal
R44, R48, R57: R_Small; R_Axial_L3.6mm_D1.6mm_P4.5mm_Horizontal
R52: 330R; R_Axial_L3.6mm_D1.6mm_P4.5mm_Horizontal
R53, R55, R56: 30R; R_Axial_DIN0204_L3.6mm_D1.6mm_P5.08mm_Horizontal
RA3, RA7: R_Network08; R_Array_SIP9
RP8: 33R; R_Array_SIP8
RP11: R_Network04; R_Array_SIP5
SPEAKER1: Conn_01x04; PinHeader_1x04_P2.54mm_Vertical
U10: ST62C303-A; PQFP-160_28x28mm_P0.65mm
U11, U18: 74LS245; DIP-20_W7.62mm
U12: 74LS00; DIP-14_W7.62mm
U15: HM6818P; DIP-24_W15.24mm_Socket
U16: 4069; DIP-14_W7.62mm
X1: 14.31818MHz; Crystal_HC50_Horizontal
X2: 32.768kHz; Crystal_AT310_D3.0mm_L10.0mm_Horizontal

Connections:
8041CS: U10.46 (8041CS)
+5V: D4.2 (A), Q3.1 (E), R45.1, R52.1, RA3.1 (common), RA7.1 (R1), RP11.1 (R1), SPEAKER1.4, U10.12 (+5V), U10.24 (+5V), U10.49 (+5V), U10.66 (+5V), U10.83 (+5V), U10.84 (+5V), U10.102 (+5V), U10.118 (+5V), U10.127 (+5V), U10.134 (+5V), U10.142 (+5V), U10.148 (+5V), U10.160 (+5V), U11.20 (VCC), U18.20 (VCC)
A1: U10.34 (A1)
A2: U10.33 (A2)
A3: U10.27 (A3)
A4: U10.26 (A4)
A5: U10.25 (A5)
A6: U10.23 (A6)
A7: U10.22 (A7)
A8: U10.21 (A8)
A9: U10.15 (A9)
A10: U10.14 (A10)
A11: U10.13 (A11)
A12: U10.11 (A12)
A13: U10.10 (A13)
A14: U10.9 (A14)
A15: U10.3 (A15)
A16: U10.1 (A16)
A17: U10.159 (A17)
A18: U10.158 (A18)
A19: U10.157 (A19)
A21: U10.151 (A21)
A22: U10.150 (A22)
A23: U10.149 (A23)
AEN: U10.152 (AEN)
BALE: U10.135 (BALE)
CHSET01: U10.137 (CHSET01)
CHSET02: U10.136 (CHSET02)
CHSET03: U10.133 (CHSET03)
CHSET04: U10.124 (CHSET04)
CHSET05: U10.123 (CHSET05)
CHSET06: U10.122 (CHSET06)
CHSET07: U10.116 (CHSET07)
CHSET08: U10.114 (CHSET08)
CHSET09: U10.113 (CHSET09)
CHSET10: U10.112 (CHSET10)
CHSET11: U10.101 (CHSET11)
CHSET12: U10.100 (CHSET12)
CHSET13: U10.99 (CHSET13)
CHSET14: U10.2 (CHSET14)
DRQ0: U10.94 (DRQ0)
DRQ1: U10.93 (DRQ1)
DRQ2: U10.91 (DRQ2)
DRQ3: U10.92 (DRQ3)
DRQ5: U10.63 (DRQ5)
DRQ6: U10.64 (DRQ6)
DRQ7: U10.65 (DRQ7)
GND: BT1.2 (-), C46.1, C47.1, C58.2, C62.1, JP9.3, JP9.4, Q1.1 (E), Q2.1 (E), R46.1, SPEAKER1.3, U10.6 (GND), U10.18 (GND), U10.30 (GND), U10.40 (GND), U10.43 (GND), U10.50 (GND), U10.55 (GND), U10.80 (GND), U10.109 (GND), U10.120 (GND), U10.128 (GND), U10.141 (GND), U10.154 (GND), U11.10 (GND), U11.19 (CE), U15.12 (VSS), U16.7 (VSS), U18.10 (GND), U18.19 (CE)
INTR: U10.146 (INTR)
IOCHRDY: U10.36 (IOCHRDY)
IRQ2: U10.76 (IRQ2)
IRQ3: U10.90 (IRQ3)
IRQ4: U10.89 (IRQ4)
IRQ5: U10.88 (IRQ5)
IRQ6: U10.87 (IRQ6)
IRQ7: U10.86 (IRQ7)
IRQ10: U10.77 (IRQ10)
IRQ11: U10.78 (IRQ11)
IRQ12: U10.79 (IRQ12)
IRQ14: U10.82 (IRQ14)
IRQ15: U10.81 (IRQ15)
KBINT: U10.85 (KBINT)
LA17: U10.140 (LA17)
LA18: U10.139 (LA18)
LA19: U10.130 (LA19)
LA20: U10.129 (LA20)
LA21: U10.126 (LA21)
LA22: U10.125 (LA22)
LA23: U10.111 (LA23)
MD8: U11.9 (A7)
MD9: U11.8 (A6)
MD10: U11.7 (A5)
MD11: U11.6 (A4)
MD12: U11.5 (A3)
MD13: U11.4 (A2)
MD14: U11.3 (A1)
MD15: U11.2 (A0)
NMI: U10.147 (NMI)
unnamed: C46.2, R44.1, U10.41 (OSCIN), X1.1
unnamed: C47.2, R44.2, U10.42 (OSCOUT), X1.2
unnamed: C60.1, X2.2
unnamed: C60.2, R57.2, U16.9
unnamed: D3.2 (A), JP9.1
unnamed: D4.1 (K), R49.1
unnamed: Q1.2 (C), R11.2
unnamed: Q1.3 (B), R10.2
unnamed: Q2.2 (C), R47.1
unnamed: Q2.3 (B), R45.2, R46.2
unnamed: Q3.3 (B), R47.2
unnamed: R10.1, U10.35 (SPEAKER)
unnamed: R11.1, SPEAKER1.1
unnamed: R55.1, U10.155 (~SMEMR)
unnamed: R56.1, U10.153 (~SMEMW)
unnamed: R57.1, U16.3, U16.5, U16.8
unnamed: RA7.3 (R2.2), U12.4, U12.5, U15.19 (~IRQ)
unnamed: RP8.1 (R1.1), U10.5 (~IOW)
unnamed: RP8.3 (R2.1), U10.8 (~IOR)
unnamed: RP8.5 (R3.1), U10.144 (~MEMW)
unnamed: RP8.8 (R4.2), U10.143 (~MEMR)
unnamed: U15.2 (OSC1), U16.4
unnamed: U16.6, X2.1
OSC: U10.57 (OSC)
REFRESH: R52.2, R53.2
REFRESH_OUT: R53.1, U10.59 (REFRESH)
RESETCOP: U10.105 (RESETCOP)
RESET_jumper: U15.16 (~STBY)
RTCAS: U10.47 (RTCAS), U15.14 (AS)
RTCIRQ: U10.75 (RTCIRQ), U12.6
SA0: U10.108 (SA0)
SA1: U10.107 (SA1)
SA2: U10.56 (SA2)
SA3: U10.54 (SA3)
SA4: U10.53 (SA4)
SA5: U10.45 (SA5)
SA6: U10.44 (SA6)
SA7: U10.39 (SA7)
SA8: U10.38 (SA8)
SA9: U10.32 (SA9)
SA10: U10.31 (SA10)
SA11: U10.29 (SA11)
SA12: U10.28 (SA12)
SA13: U10.20 (SA13)
SA14: U10.19 (SA14)
SA15: U10.17 (SA15)
SA16: U10.16 (SA16)
SA17: U10.7 (SA17)
SA18: U10.4 (SA18)
SA19: U10.156 (SA19)
SD0: U18.18 (B0)
SD1: U18.17 (B1)
SD2: U18.16 (B2)
SD3: U18.15 (B3)
SD4: U18.14 (B4)
SD5: U18.13 (B5)
SD6: U18.12 (B6)
SD7: U18.11 (B7)
SD8: RA3.5 (R4), U11.11 (B7)
SD9: RA3.4 (R3), U11.12 (B6)
SD10: RA3.3 (R2), U11.13 (B5)
SD11: RA3.2 (R1), U11.14 (B4)
SD12: RA3.9 (R8), U11.15 (B3)
SD13: RA3.8 (R7), U11.16 (B2)
SD14: RA3.7 (R6), U11.17 (B1)
SD15: RA3.6 (R5), U11.18 (B0)
SDDIR: U11.1 (A->B)
SW1-4: U10.115
SYSCLK: U10.117 (SYSCLK)
SYSRESET: U10.121 (SYSRESET)
TC: U10.52 (TC)
VBAT: C58.1, D2.1 (K), Q3.2 (C), R48.1, U15.20 (CKFS), U15.24 (VDD), U16.14 (VDD)
XD0: U10.74 (XD0), U15.4 (AD0), U18.2 (A0)
XD1: U10.73 (XD1), U15.5 (AD1), U18.3 (A1)
XD2: U10.72 (XD2), U15.6 (AD2), U18.4 (A2)
XD3: U10.71 (XD3), U15.7 (AD3), U18.5 (A3)
XD4: U10.70 (XD4), U15.8 (AD4), U18.6 (A4)
XD5: U10.69 (XD5), U15.9 (AD5), U18.7 (A5)
XD6: U10.68 (XD6), U15.10 (AD6), U18.8 (A6)
XD7: U10.67 (XD7), U15.11 (AD7), U18.9 (A7)
XDDIR: U18.1 (A->B)
bat+: BT1.1 (+), D2.2 (A), D3.1 (K), R49.2
c62-2: C62.2, R48.2, U15.18 (~RESET), U15.22 (PS)
rp11-5: RP11.5 (R4.2), U10.119
~BUSYCOP: U10.104 (~BUSYCOP)
~BUSY_CHSET: U10.145 (~BUSYCPU)
~DACK0: U10.98 (~DACK0)
~DACK1: U10.96 (~DACK1)
~DACK2: U10.97 (~DACK2)
~DACK3: U10.95 (~DACK3)
~DACK5: U10.60 (~DACK5)
~DACK6: U10.61 (~DACK6)
~DACK7: U10.62 (~DACK7)
~IOCHK: U10.37 (~IOCHK)
~IOR: RP8.4 (R2.2)
~IOW: RP8.2 (R1.2)
~MASTER: U10.58 (~MASTER)
~MEMR: RP8.7 (R4.1)
~MEMW: RP8.6 (R3.2)
~NPERROR: U10.103 (~NPERROR)
~NPS1: U10.138 (~NPS1)
~RTCCE: U15.13 (~CE)
~RTCRD: U10.51 (~RTCRD), U15.17 (DS)
~RTCWR: U10.48 (~RTCWR), U15.15 (R/~W)
~SBHE: U10.110 (~SBHE)
~SMEMR: R55.2
~SMEMW: R56.2
~XIOR: U10.131 (~XIOR)
~XIOW: U10.132 (~XIOW)
