TomasPavlovicPavlo/286_schematic/KiCAD/FLOPPY_IDE.kicad_sch

## KiCad design KiCAD/FLOPPY_IDE.kicad_sch (2025-07-11)

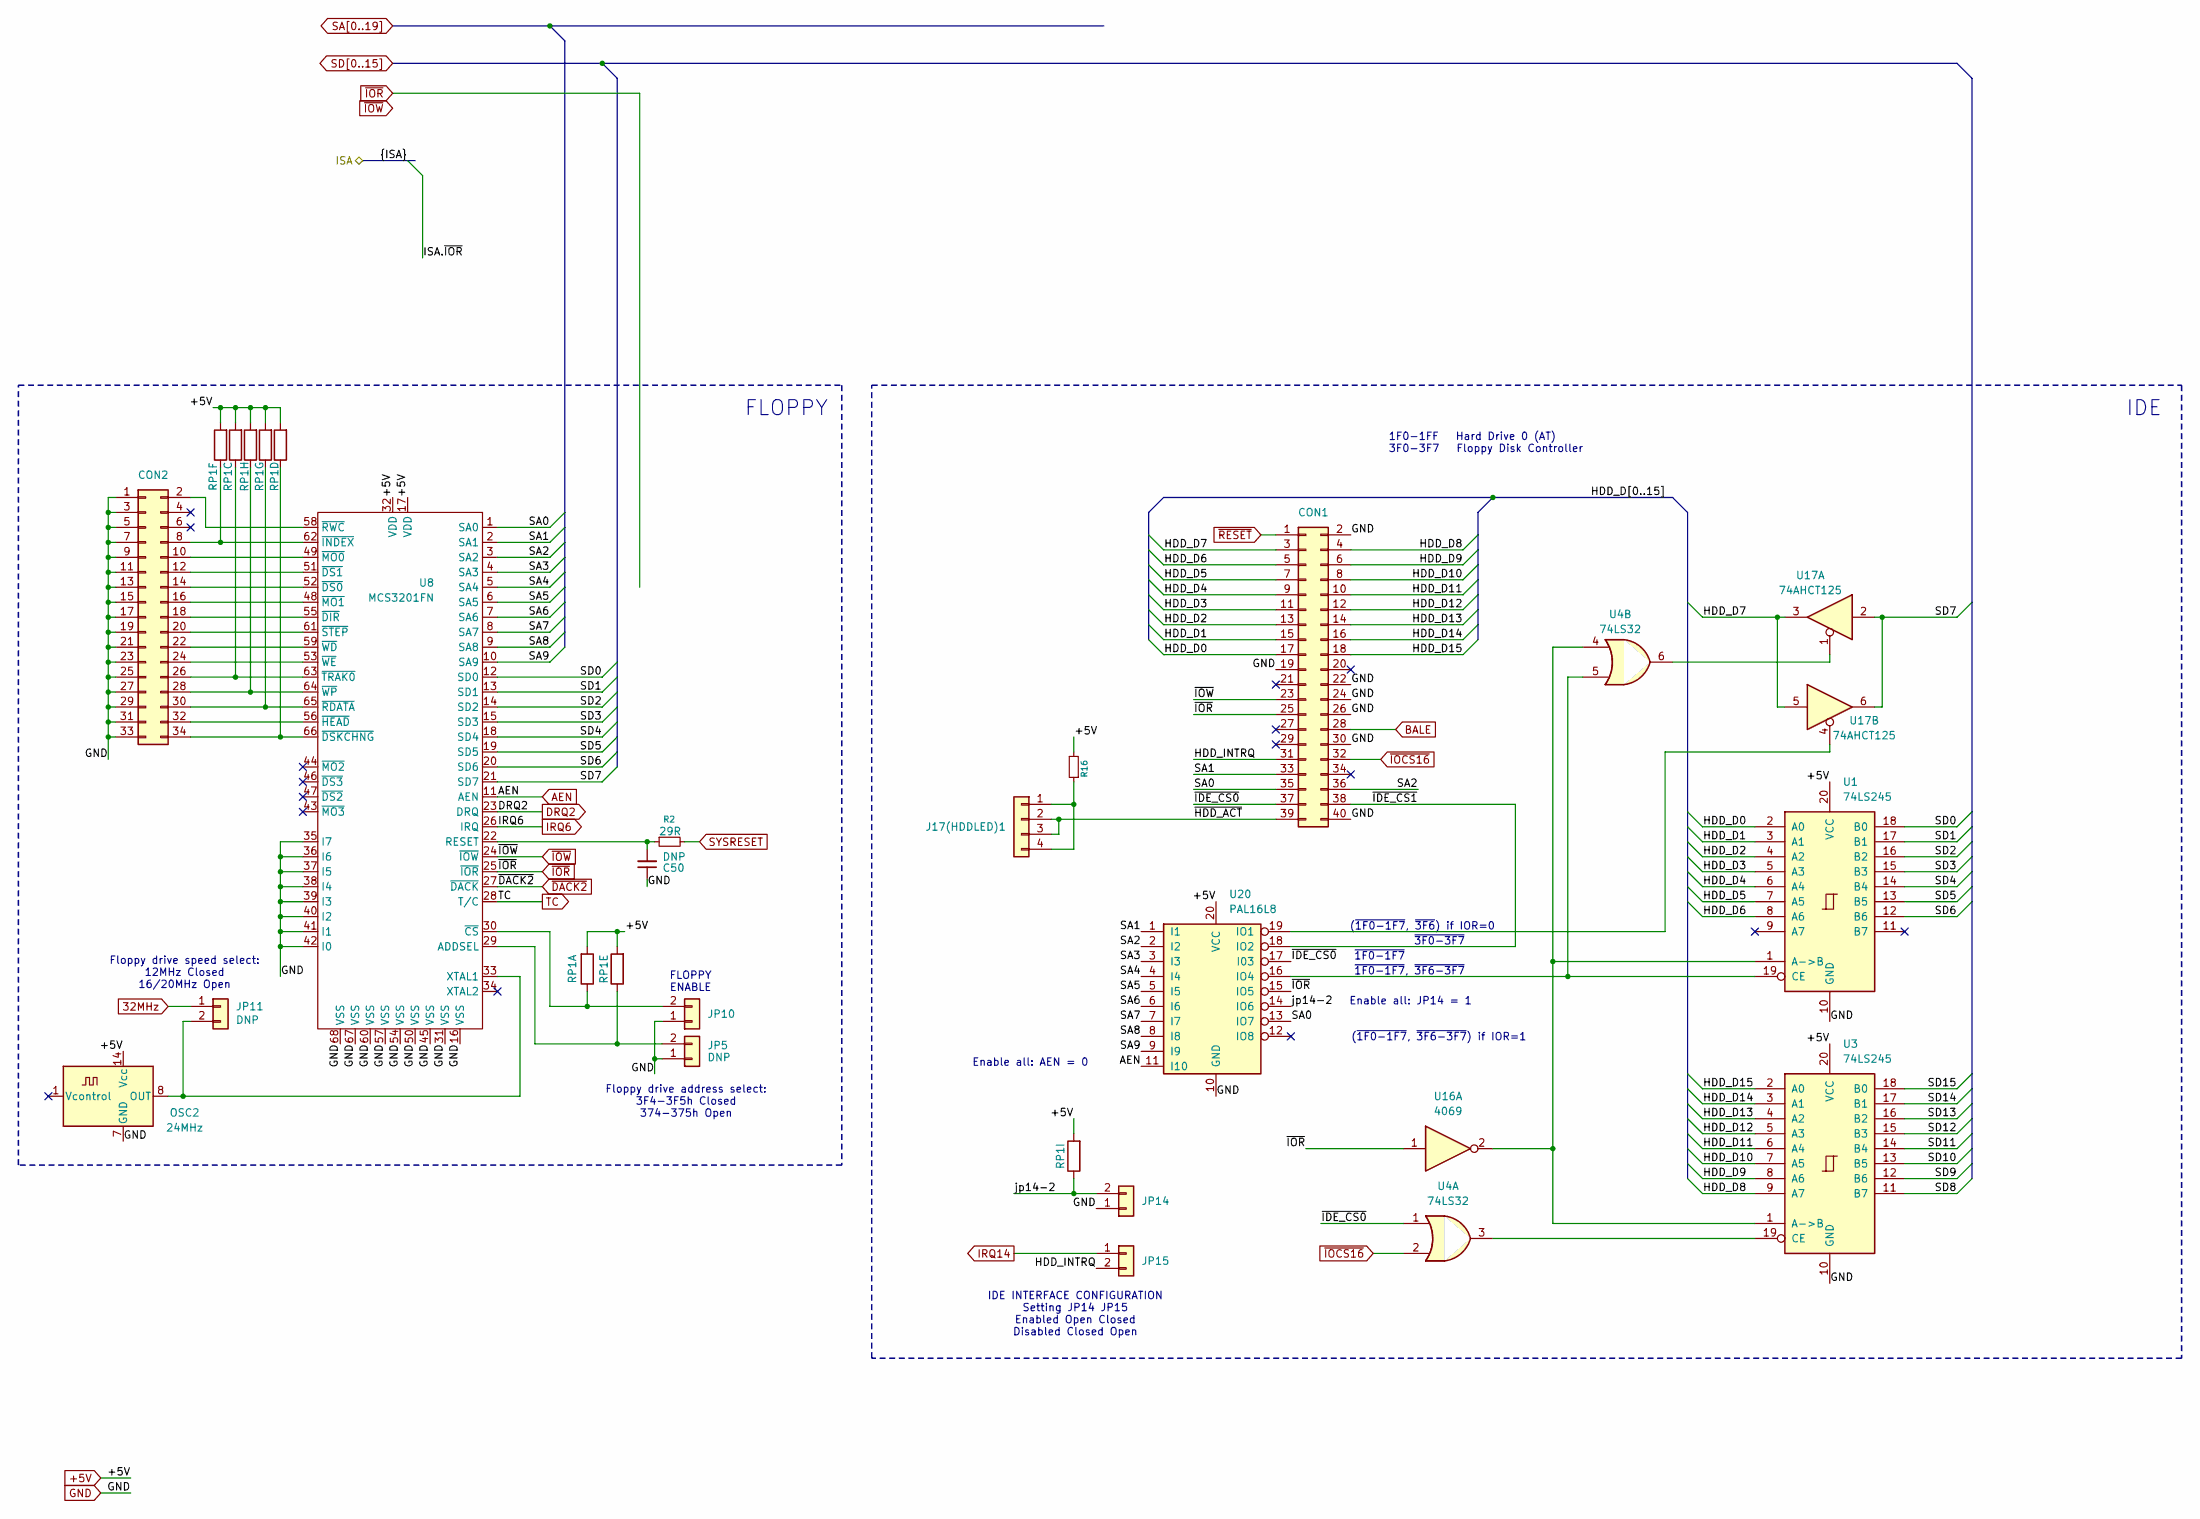
[picture p32: schematic FLOPPY_IDE.kicad_sch]

Parts:
C50: DNP; C_Disc_D4.3mm_W1.9mm_P5.00mm
CON1: Conn_02x20_Odd_Even; PinHeader_2x20_P2.54mm_Vertical
CON2: Conn_02x17_Odd_Even; PinHeader_2x17_P2.54mm_Vertical
J17(HDDLED)1: Conn_01x04; PinHeader_1x04_P2.54mm_Vertical
JP5, JP11: DNP; PinSocket_1x02_P2.54mm_Vertical
JP10, JP14, JP15: Conn_01x02; PinSocket_1x02_P2.54mm_Vertical
OSC2: 24MHz; Oscillator_DIP-14
R2: 29R; R_Axial_DIN0204_L3.6mm_D1.6mm_P5.08mm_Horizontal
R16: R_Small; R_Axial_L3.6mm_D1.6mm_P4.5mm_Horizontal
RP1: R_Network09; R_Array_SIP10
U1, U3: 74LS245; DIP-20_W7.62mm
U4: 74LS32; DIP-14_W7.62mm
U8: MCS3201FN; PLCC-68
U16: 4069; DIP-14_W7.62mm
U17: 74AHCT125; DIP-14_W7.62mm
U20: PAL16L8; DIP-20_W7.62mm

Connections:
32MHz: JP11.1
+5V: OSC2.14 (Vcc), R16.2, RP1.1 (R1), U1.20 (VCC), U3.20 (VCC), U8.17 (VDD), U8.32 (VDD), U20.20 (VCC)
AEN: U8.11 (AEN), U20.11 (I10)
BALE: CON1.28
DRQ2: U8.23 (DRQ)
GND: C50.1, CON1.2, CON1.19, CON1.22, CON1.24, CON1.26, CON1.30, CON1.40, CON2.1, CON2.3, CON2.5, CON2.7, CON2.9, CON2.11, CON2.13, CON2.15, CON2.17, CON2.19, CON2.21, CON2.23, CON2.25, CON2.27, CON2.29, CON2.31, CON2.33, JP5.1, JP10.1, JP14.1, OSC2.7 (GND), U1.10 (GND), U3.10 (GND), U8.16 (VSS), U8.31 (VSS), U8.35 (I7), U8.36 (I6), U8.37 (I5), U8.38 (I4), U8.39 (I3), U8.40 (I2), U8.41 (I1), U8.42 (I0), U8.45 (VSS), U8.50 (VSS), U8.54 (VSS), U8.57 (VSS), U8.60 (VSS), U8.67 (VSS), U8.68 (VSS), U20.10 (GND)
HDD_D0: CON1.17, U1.2 (A0)
HDD_D1: CON1.15, U1.3 (A1)
HDD_D2: CON1.13, U1.4 (A2)
HDD_D3: CON1.11, U1.5 (A3)
HDD_D4: CON1.9, U1.6 (A4)
HDD_D5: CON1.7, U1.7 (A5)
HDD_D6: CON1.5, U1.8 (A6)
HDD_D7: CON1.3, U17.3, U17.5
HDD_D8: CON1.4, U3.9 (A7)
HDD_D9: CON1.6, U3.8 (A6)
HDD_D10: CON1.8, U3.7 (A5)
HDD_D11: CON1.10, U3.6 (A4)
HDD_D12: CON1.12, U3.5 (A3)
HDD_D13: CON1.14, U3.4 (A2)
HDD_D14: CON1.16, U3.3 (A1)
HDD_D15: CON1.18, U3.2 (A0)
HDD_INTRQ: CON1.31, JP15.2
IRQ6: U8.26 (IRQ)
IRQ14: JP15.1
unnamed: C50.2, R2.1, U8.22 (RESET)
unnamed: CON2.2, U8.58 (~RWC)
unnamed: CON2.8, RP1.7 (R6.2), U8.62 (~INDEX)
unnamed: CON2.10, U8.49 (~MO0)
unnamed: CON2.12, U8.51 (~DS1)
unnamed: CON2.14, U8.52 (~DS0)
unnamed: CON2.16, U8.48 (~MO1)
unnamed: CON2.18, U8.55 (~DIR)
unnamed: CON2.20, U8.61 (~STEP)
unnamed: CON2.22, U8.59 (~WD)
unnamed: CON2.24, U8.53 (~WE)
unnamed: CON2.26, RP1.4 (R3.2), U8.63 (~TRAK0)
unnamed: CON2.28, RP1.9 (R8.2), U8.64 (~WP)
unnamed: CON2.30, RP1.8 (R7.2), U8.65 (~RDATA)
unnamed: CON2.32, U8.56 (~HEAD)
unnamed: CON2.34, RP1.5 (R4.2), U8.66 (~DSKCHNG)
unnamed: J17(HDDLED)1.1, J17(HDDLED)1.4, R16.1
unnamed: JP5.2, RP1.6 (R5.2), U8.29 (ADDSEL)
unnamed: JP10.2, RP1.2 (R1.2), U8.30 (~CS)
unnamed: JP11.2, OSC2.8 (OUT), U8.33 (XTAL1)
unnamed: U1.1 (A->B), U3.1 (A->B), U4.4, U16.2
unnamed: U1.19 (CE), U4.5, U20.16 (IO4)
unnamed: U3.19 (CE), U4.3
unnamed: U4.6, U17.1
unnamed: U17.4, U20.19 (IO1)
SA0: CON1.35, U8.1 (SA0), U20.13 (IO7)
SA1: CON1.33, U8.2 (SA1), U20.1 (I1)
SA2: CON1.36, U8.3 (SA2), U20.2 (I2)
SA3: U8.4 (SA3), U20.3 (I3)
SA4: U8.5 (SA4), U20.4 (I4)
SA5: U8.6 (SA5), U20.5 (I5)
SA6: U8.7 (SA6), U20.6 (I6)
SA7: U8.8 (SA7), U20.7 (I7)
SA8: U8.9 (SA8), U20.8 (I8)
SA9: U8.10 (SA9), U20.9 (I9)
SD0: U1.18 (B0), U8.12 (SD0)
SD1: U1.17 (B1), U8.13 (SD1)
SD2: U1.16 (B2), U8.14 (SD2)
SD3: U1.15 (B3), U8.15 (SD3)
SD4: U1.14 (B4), U8.18 (SD4)
SD5: U1.13 (B5), U8.19 (SD5)
SD6: U1.12 (B6), U8.20 (SD6)
SD7: U8.21 (SD7), U17.2, U17.6
SD8: U3.11 (B7)
SD9: U3.12 (B6)
SD10: U3.13 (B5)
SD11: U3.14 (B4)
SD12: U3.15 (B3)
SD13: U3.16 (B2)
SD14: U3.17 (B1)
SD15: U3.18 (B0)
SYSRESET: R2.2
TC: U8.28 (T/C)
jp14-2: JP14.2, RP1.10 (R9.2), U20.14 (IO6)
~DACK2: U8.27 (~DACK)
~HDD_ACT: CON1.39, J17(HDDLED)1.2, J17(HDDLED)1.3
~IDE_CS0: CON1.37, U4.1, U20.17 (I03)
~IDE_CS1: CON1.38, U20.18 (IO2)
~IOCS16: CON1.32, U4.2
~IOR: CON1.25, U8.25 (~IOR), U16.1, U20.15 (IO5)
~IOW: CON1.23, U8.24 (~IOW)
~RESET: CON1.1

Notes on the sheet:
~{1F0-1F7}, ~{3F6-3F7}
(~{1F0-1F7}, ~{3F6}) if IOR=0
IDE
Floppy drive address select: 3F4-3F5h Closed 374-375h Open
Enable all: AEN = 0
Enable all: JP14 = 1
FLOPPY ENABLE
(~{1F0-1F7}, ~{3F6-3F7}) if IOR=1
1F0-1FF Hard Drive 0 (AT) 3F0-3F7 Floppy Disk Controller
Floppy drive speed select: 12MHz Closed 16/20MHz Open
~{3F0-3F7}
~{1F0-1F7}
FLOPPY
IDE INTERFACE CONFIGURATION Setting JP14 JP15 Enabled Open Closed Disabled Closed Open
