TomasPavlovicPavlo/286_schematic/KiCAD/ISA.kicad_sch

## KiCad design KiCAD/ISA.kicad_sch (2025-06-28)

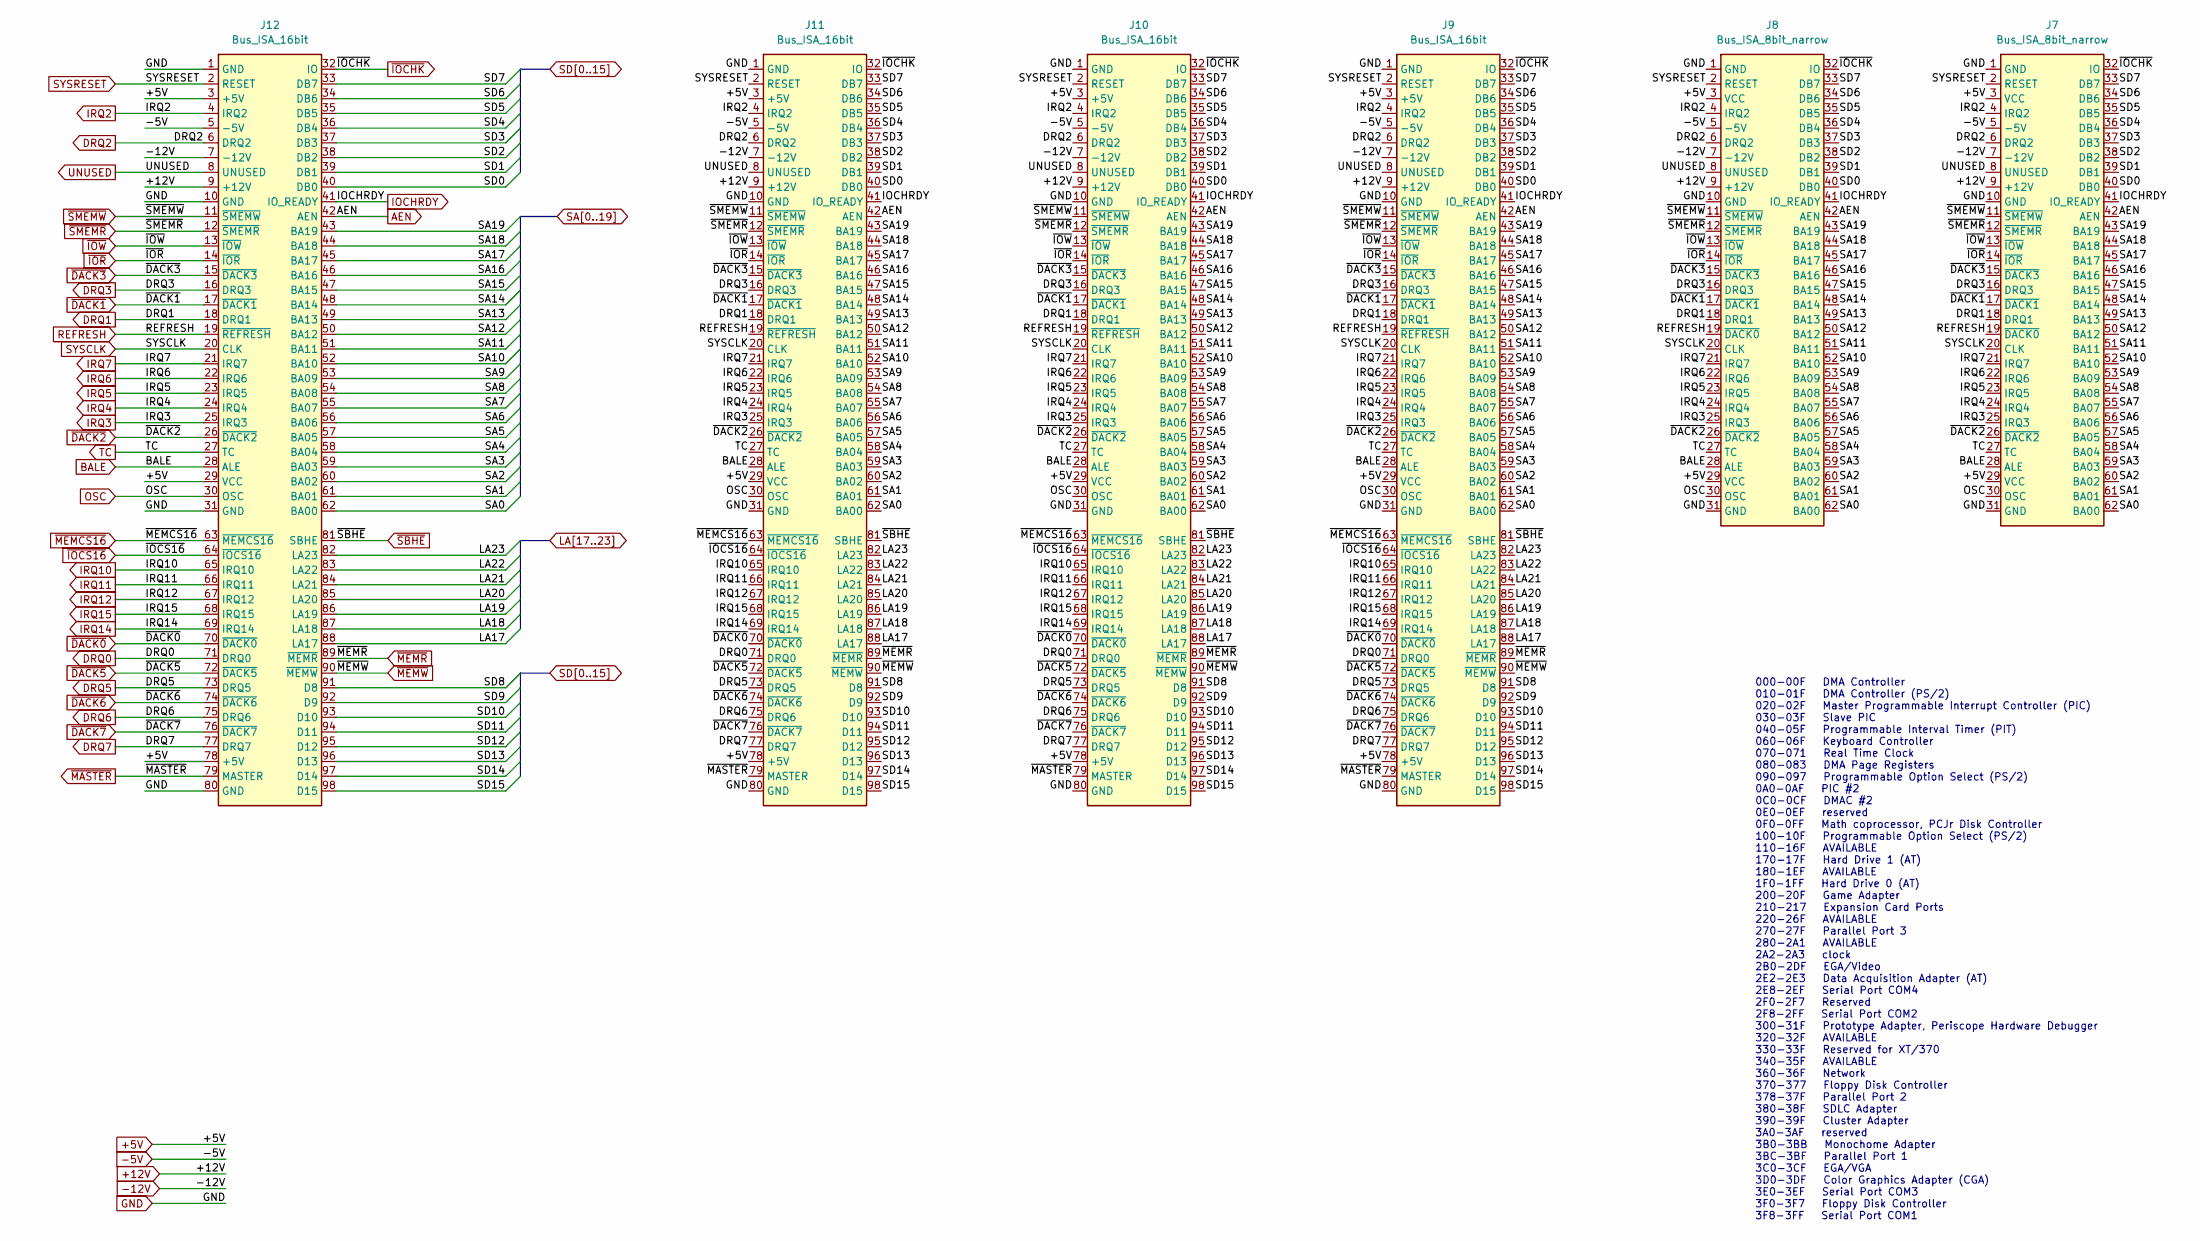
[picture p33: schematic ISA.kicad_sch]

Parts:
J7, J8: Bus_ISA_8bit_narrow; ISA_8bit
J9, J10, J11, J12: Bus_ISA_16bit; ISA_16bit

Connections:
+5V: J7.3 (VCC), J7.29 (VCC), J8.3 (VCC), J8.29 (VCC), J9.3 (+5V), J9.29 (VCC), J9.78 (+5V), J10.3 (+5V), J10.29 (VCC), J10.78 (+5V), J11.3 (+5V), J11.29 (VCC), J11.78 (+5V), J12.3 (+5V), J12.29 (VCC), J12.78 (+5V)
+12V: J7.9 (+12V), J8.9 (+12V), J9.9 (+12V), J10.9 (+12V), J11.9 (+12V), J12.9 (+12V)
-5V: J7.5 (-5V), J8.5 (-5V), J9.5 (-5V), J10.5 (-5V), J11.5 (-5V), J12.5 (-5V)
-12V: J7.7 (-12V), J8.7 (-12V), J9.7 (-12V), J10.7 (-12V), J11.7 (-12V), J12.7 (-12V)
AEN: J7.42 (AEN), J8.42 (AEN), J9.42 (AEN), J10.42 (AEN), J11.42 (AEN), J12.42 (AEN)
BALE: J7.28 (ALE), J8.28 (ALE), J9.28 (ALE), J10.28 (ALE), J11.28 (ALE), J12.28 (ALE)
DRQ0: J9.71 (DRQ0), J10.71 (DRQ0), J11.71 (DRQ0), J12.71 (DRQ0)
DRQ1: J7.18 (DRQ1), J8.18 (DRQ1), J9.18 (DRQ1), J10.18 (DRQ1), J11.18 (DRQ1), J12.18 (DRQ1)
DRQ2: J7.6 (DRQ2), J8.6 (DRQ2), J9.6 (DRQ2), J10.6 (DRQ2), J11.6 (DRQ2), J12.6 (DRQ2)
DRQ3: J7.16 (DRQ3), J8.16 (DRQ3), J9.16 (DRQ3), J10.16 (DRQ3), J11.16 (DRQ3), J12.16 (DRQ3)
DRQ5: J9.73 (DRQ5), J10.73 (DRQ5), J11.73 (DRQ5), J12.73 (DRQ5)
DRQ6: J9.75 (DRQ6), J10.75 (DRQ6), J11.75 (DRQ6), J12.75 (DRQ6)
DRQ7: J9.77 (DRQ7), J10.77 (DRQ7), J11.77 (DRQ7), J12.77 (DRQ7)
GND: J7.1 (GND), J7.10 (GND), J7.31 (GND), J8.1 (GND), J8.10 (GND), J8.31 (GND), J9.1 (GND), J9.10 (GND), J9.31 (GND), J9.80 (GND), J10.1 (GND), J10.10 (GND), J10.31 (GND), J10.80 (GND), J11.1 (GND), J11.10 (GND), J11.31 (GND), J11.80 (GND), J12.1 (GND), J12.10 (GND), J12.31 (GND), J12.80 (GND)
IOCHRDY: J7.41 (IO_READY), J8.41 (IO_READY), J9.41 (IO_READY), J10.41 (IO_READY), J11.41 (IO_READY), J12.41 (IO_READY)
IRQ2: J7.4 (IRQ2), J8.4 (IRQ2), J9.4 (IRQ2), J10.4 (IRQ2), J11.4 (IRQ2), J12.4 (IRQ2)
IRQ3: J7.25 (IRQ3), J8.25 (IRQ3), J9.25 (IRQ3), J10.25 (IRQ3), J11.25 (IRQ3), J12.25 (IRQ3)
IRQ4: J7.24 (IRQ4), J8.24 (IRQ4), J9.24 (IRQ4), J10.24 (IRQ4), J11.24 (IRQ4), J12.24 (IRQ4)
IRQ5: J7.23 (IRQ5), J8.23 (IRQ5), J9.23 (IRQ5), J10.23 (IRQ5), J11.23 (IRQ5), J12.23 (IRQ5)
IRQ6: J7.22 (IRQ6), J8.22 (IRQ6), J9.22 (IRQ6), J10.22 (IRQ6), J11.22 (IRQ6), J12.22 (IRQ6)
IRQ7: J7.21 (IRQ7), J8.21 (IRQ7), J9.21 (IRQ7), J10.21 (IRQ7), J11.21 (IRQ7), J12.21 (IRQ7)
IRQ10: J9.65 (IRQ10), J10.65 (IRQ10), J11.65 (IRQ10), J12.65 (IRQ10)
IRQ11: J9.66 (IRQ11), J10.66 (IRQ11), J11.66 (IRQ11), J12.66 (IRQ11)
IRQ12: J9.67 (IRQ12), J10.67 (IRQ12), J11.67 (IRQ12), J12.67 (IRQ12)
IRQ14: J9.69 (IRQ14), J10.69 (IRQ14), J11.69 (IRQ14), J12.69 (IRQ14)
IRQ15: J9.68 (IRQ15), J10.68 (IRQ15), J11.68 (IRQ15), J12.68 (IRQ15)
LA17: J9.88 (LA17), J10.88 (LA17), J11.88 (LA17), J12.88 (LA17)
LA18: J9.87 (LA18), J10.87 (LA18), J11.87 (LA18), J12.87 (LA18)
LA19: J9.86 (LA19), J10.86 (LA19), J11.86 (LA19), J12.86 (LA19)
LA20: J9.85 (LA20), J10.85 (LA20), J11.85 (LA20), J12.85 (LA20)
LA21: J9.84 (LA21), J10.84 (LA21), J11.84 (LA21), J12.84 (LA21)
LA22: J9.83 (LA22), J10.83 (LA22), J11.83 (LA22), J12.83 (LA22)
LA23: J9.82 (LA23), J10.82 (LA23), J11.82 (LA23), J12.82 (LA23)
OSC: J7.30 (OSC), J8.30 (OSC), J9.30 (OSC), J10.30 (OSC), J11.30 (OSC), J12.30 (OSC)
REFRESH: J7.19 (~DACK0), J8.19 (~DACK0), J9.19 (~REFRESH), J10.19 (~REFRESH), J11.19 (~REFRESH), J12.19 (~REFRESH)
SA0: J7.62 (BA00), J8.62 (BA00), J9.62 (BA00), J10.62 (BA00), J11.62 (BA00), J12.62 (BA00)
SA1: J7.61 (BA01), J8.61 (BA01), J9.61 (BA01), J10.61 (BA01), J11.61 (BA01), J12.61 (BA01)
SA2: J7.60 (BA02), J8.60 (BA02), J9.60 (BA02), J10.60 (BA02), J11.60 (BA02), J12.60 (BA02)
SA3: J7.59 (BA03), J8.59 (BA03), J9.59 (BA03), J10.59 (BA03), J11.59 (BA03), J12.59 (BA03)
SA4: J7.58 (BA04), J8.58 (BA04), J9.58 (BA04), J10.58 (BA04), J11.58 (BA04), J12.58 (BA04)
SA5: J7.57 (BA05), J8.57 (BA05), J9.57 (BA05), J10.57 (BA05), J11.57 (BA05), J12.57 (BA05)
SA6: J7.56 (BA06), J8.56 (BA06), J9.56 (BA06), J10.56 (BA06), J11.56 (BA06), J12.56 (BA06)
SA7: J7.55 (BA07), J8.55 (BA07), J9.55 (BA07), J10.55 (BA07), J11.55 (BA07), J12.55 (BA07)
SA8: J7.54 (BA08), J8.54 (BA08), J9.54 (BA08), J10.54 (BA08), J11.54 (BA08), J12.54 (BA08)
SA9: J7.53 (BA09), J8.53 (BA09), J9.53 (BA09), J10.53 (BA09), J11.53 (BA09), J12.53 (BA09)
SA10: J7.52 (BA10), J8.52 (BA10), J9.52 (BA10), J10.52 (BA10), J11.52 (BA10), J12.52 (BA10)
SA11: J7.51 (BA11), J8.51 (BA11), J9.51 (BA11), J10.51 (BA11), J11.51 (BA11), J12.51 (BA11)
SA12: J7.50 (BA12), J8.50 (BA12), J9.50 (BA12), J10.50 (BA12), J11.50 (BA12), J12.50 (BA12)
SA13: J7.49 (BA13), J8.49 (BA13), J9.49 (BA13), J10.49 (BA13), J11.49 (BA13), J12.49 (BA13)
SA14: J7.48 (BA14), J8.48 (BA14), J9.48 (BA14), J10.48 (BA14), J11.48 (BA14), J12.48 (BA14)
SA15: J7.47 (BA15), J8.47 (BA15), J9.47 (BA15), J10.47 (BA15), J11.47 (BA15), J12.47 (BA15)
SA16: J7.46 (BA16), J8.46 (BA16), J9.46 (BA16), J10.46 (BA16), J11.46 (BA16), J12.46 (BA16)
SA17: J7.45 (BA17), J8.45 (BA17), J9.45 (BA17), J10.45 (BA17), J11.45 (BA17), J12.45 (BA17)
SA18: J7.44 (BA18), J8.44 (BA18), J9.44 (BA18), J10.44 (BA18), J11.44 (BA18), J12.44 (BA18)
SA19: J7.43 (BA19), J8.43 (BA19), J9.43 (BA19), J10.43 (BA19), J11.43 (BA19), J12.43 (BA19)
SD0: J7.40 (DB0), J8.40 (DB0), J9.40 (DB0), J10.40 (DB0), J11.40 (DB0), J12.40 (DB0)
SD1: J7.39 (DB1), J8.39 (DB1), J9.39 (DB1), J10.39 (DB1), J11.39 (DB1), J12.39 (DB1)
SD2: J7.38 (DB2), J8.38 (DB2), J9.38 (DB2), J10.38 (DB2), J11.38 (DB2), J12.38 (DB2)
SD3: J7.37 (DB3), J8.37 (DB3), J9.37 (DB3), J10.37 (DB3), J11.37 (DB3), J12.37 (DB3)
SD4: J7.36 (DB4), J8.36 (DB4), J9.36 (DB4), J10.36 (DB4), J11.36 (DB4), J12.36 (DB4)
SD5: J7.35 (DB5), J8.35 (DB5), J9.35 (DB5), J10.35 (DB5), J11.35 (DB5), J12.35 (DB5)
SD6: J7.34 (DB6), J8.34 (DB6), J9.34 (DB6), J10.34 (DB6), J11.34 (DB6), J12.34 (DB6)
SD7: J7.33 (DB7), J8.33 (DB7), J9.33 (DB7), J10.33 (DB7), J11.33 (DB7), J12.33 (DB7)
SD8: J9.91 (D8), J10.91 (D8), J11.91 (D8), J12.91 (D8)
SD9: J9.92 (D9), J10.92 (D9), J11.92 (D9), J12.92 (D9)
SD10: J9.93 (D10), J10.93 (D10), J11.93 (D10), J12.93 (D10)
SD11: J9.94 (D11), J10.94 (D11), J11.94 (D11), J12.94 (D11)
SD12: J9.95 (D12), J10.95 (D12), J11.95 (D12), J12.95 (D12)
SD13: J9.96 (D13), J10.96 (D13), J11.96 (D13), J12.96 (D13)
SD14: J9.97 (D14), J10.97 (D14), J11.97 (D14), J12.97 (D14)
SD15: J9.98 (D15), J10.98 (D15), J11.98 (D15), J12.98 (D15)
SYSCLK: J7.20 (CLK), J8.20 (CLK), J9.20 (CLK), J10.20 (CLK), J11.20 (CLK), J12.20 (CLK)
SYSRESET: J7.2 (RESET), J8.2 (RESET), J9.2 (RESET), J10.2 (RESET), J11.2 (RESET), J12.2 (RESET)
TC: J7.27 (TC), J8.27 (TC), J9.27 (TC), J10.27 (TC), J11.27 (TC), J12.27 (TC)
UNUSED: J7.8 (UNUSED), J8.8 (UNUSED), J9.8 (UNUSED), J10.8 (UNUSED), J11.8 (UNUSED), J12.8 (UNUSED)
~DACK0: J9.70 (~DACK0), J10.70 (~DACK0), J11.70 (~DACK0), J12.70 (~DACK0)
~DACK1: J7.17 (~DACK1), J8.17 (~DACK1), J9.17 (~DACK1), J10.17 (~DACK1), J11.17 (~DACK1), J12.17 (~DACK1)
~DACK2: J7.26 (~DACK2), J8.26 (~DACK2), J9.26 (~DACK2), J10.26 (~DACK2), J11.26 (~DACK2), J12.26 (~DACK2)
~DACK3: J7.15 (~DACK3), J8.15 (~DACK3), J9.15 (~DACK3), J10.15 (~DACK3), J11.15 (~DACK3), J12.15 (~DACK3)
~DACK5: J9.72 (~DACK5), J10.72 (~DACK5), J11.72 (~DACK5), J12.72 (~DACK5)
~DACK6: J9.74 (~DACK6), J10.74 (~DACK6), J11.74 (~DACK6), J12.74 (~DACK6)
~DACK7: J9.76 (~DACK7), J10.76 (~DACK7), J11.76 (~DACK7), J12.76 (~DACK7)
~IOCHK: J7.32 (IO), J8.32 (IO), J9.32 (IO), J10.32 (IO), J11.32 (IO), J12.32 (IO)
~IOCS16: J9.64 (~IOCS16), J10.64 (~IOCS16), J11.64 (~IOCS16), J12.64 (~IOCS16)
~IOR: J7.14 (~IOR), J8.14 (~IOR), J9.14 (~IOR), J10.14 (~IOR), J11.14 (~IOR), J12.14 (~IOR)
~IOW: J7.13 (~IOW), J8.13 (~IOW), J9.13 (~IOW), J10.13 (~IOW), J11.13 (~IOW), J12.13 (~IOW)
~MASTER: J9.79 (MASTER), J10.79 (MASTER), J11.79 (MASTER), J12.79 (MASTER)
~MEMCS16: J9.63 (~MEMCS16), J10.63 (~MEMCS16), J11.63 (~MEMCS16), J12.63 (~MEMCS16)
~MEMR: J9.89 (~MEMR), J10.89 (~MEMR), J11.89 (~MEMR), J12.89 (~MEMR)
~MEMW: J9.90 (~MEMW), J10.90 (~MEMW), J11.90 (~MEMW), J12.90 (~MEMW)
~SBHE: J9.81 (SBHE), J10.81 (SBHE), J11.81 (SBHE), J12.81 (SBHE)
~SMEMR: J7.12 (~SMEMR), J8.12 (~SMEMR), J9.12 (~SMEMR), J10.12 (~SMEMR), J11.12 (~SMEMR), J12.12 (~SMEMR)
~SMEMW: J7.11 (~SMEMW), J8.11 (~SMEMW), J9.11 (~SMEMW), J10.11 (~SMEMW), J11.11 (~SMEMW), J12.11 (~SMEMW)

Notes on the sheet:
000-00F DMA Controller 010-01F DMA Controller (PS/2) 020-02F Master Programmable Interrupt Controller (PIC) 030-03F Slave PIC 040-05F Programmable Interval Timer (PIT) 060-06F Keyboard Controller 070-071 Real Time Clock 080-083 DMA Page Registers 090-097 Programmable Option Select (PS/2) 0A0-0AF PI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
