TomasPavlovicPavlo/286_schematic/KiCAD/Memory.kicad_sch

## KiCad design KiCAD/Memory.kicad_sch (2025-06-28)

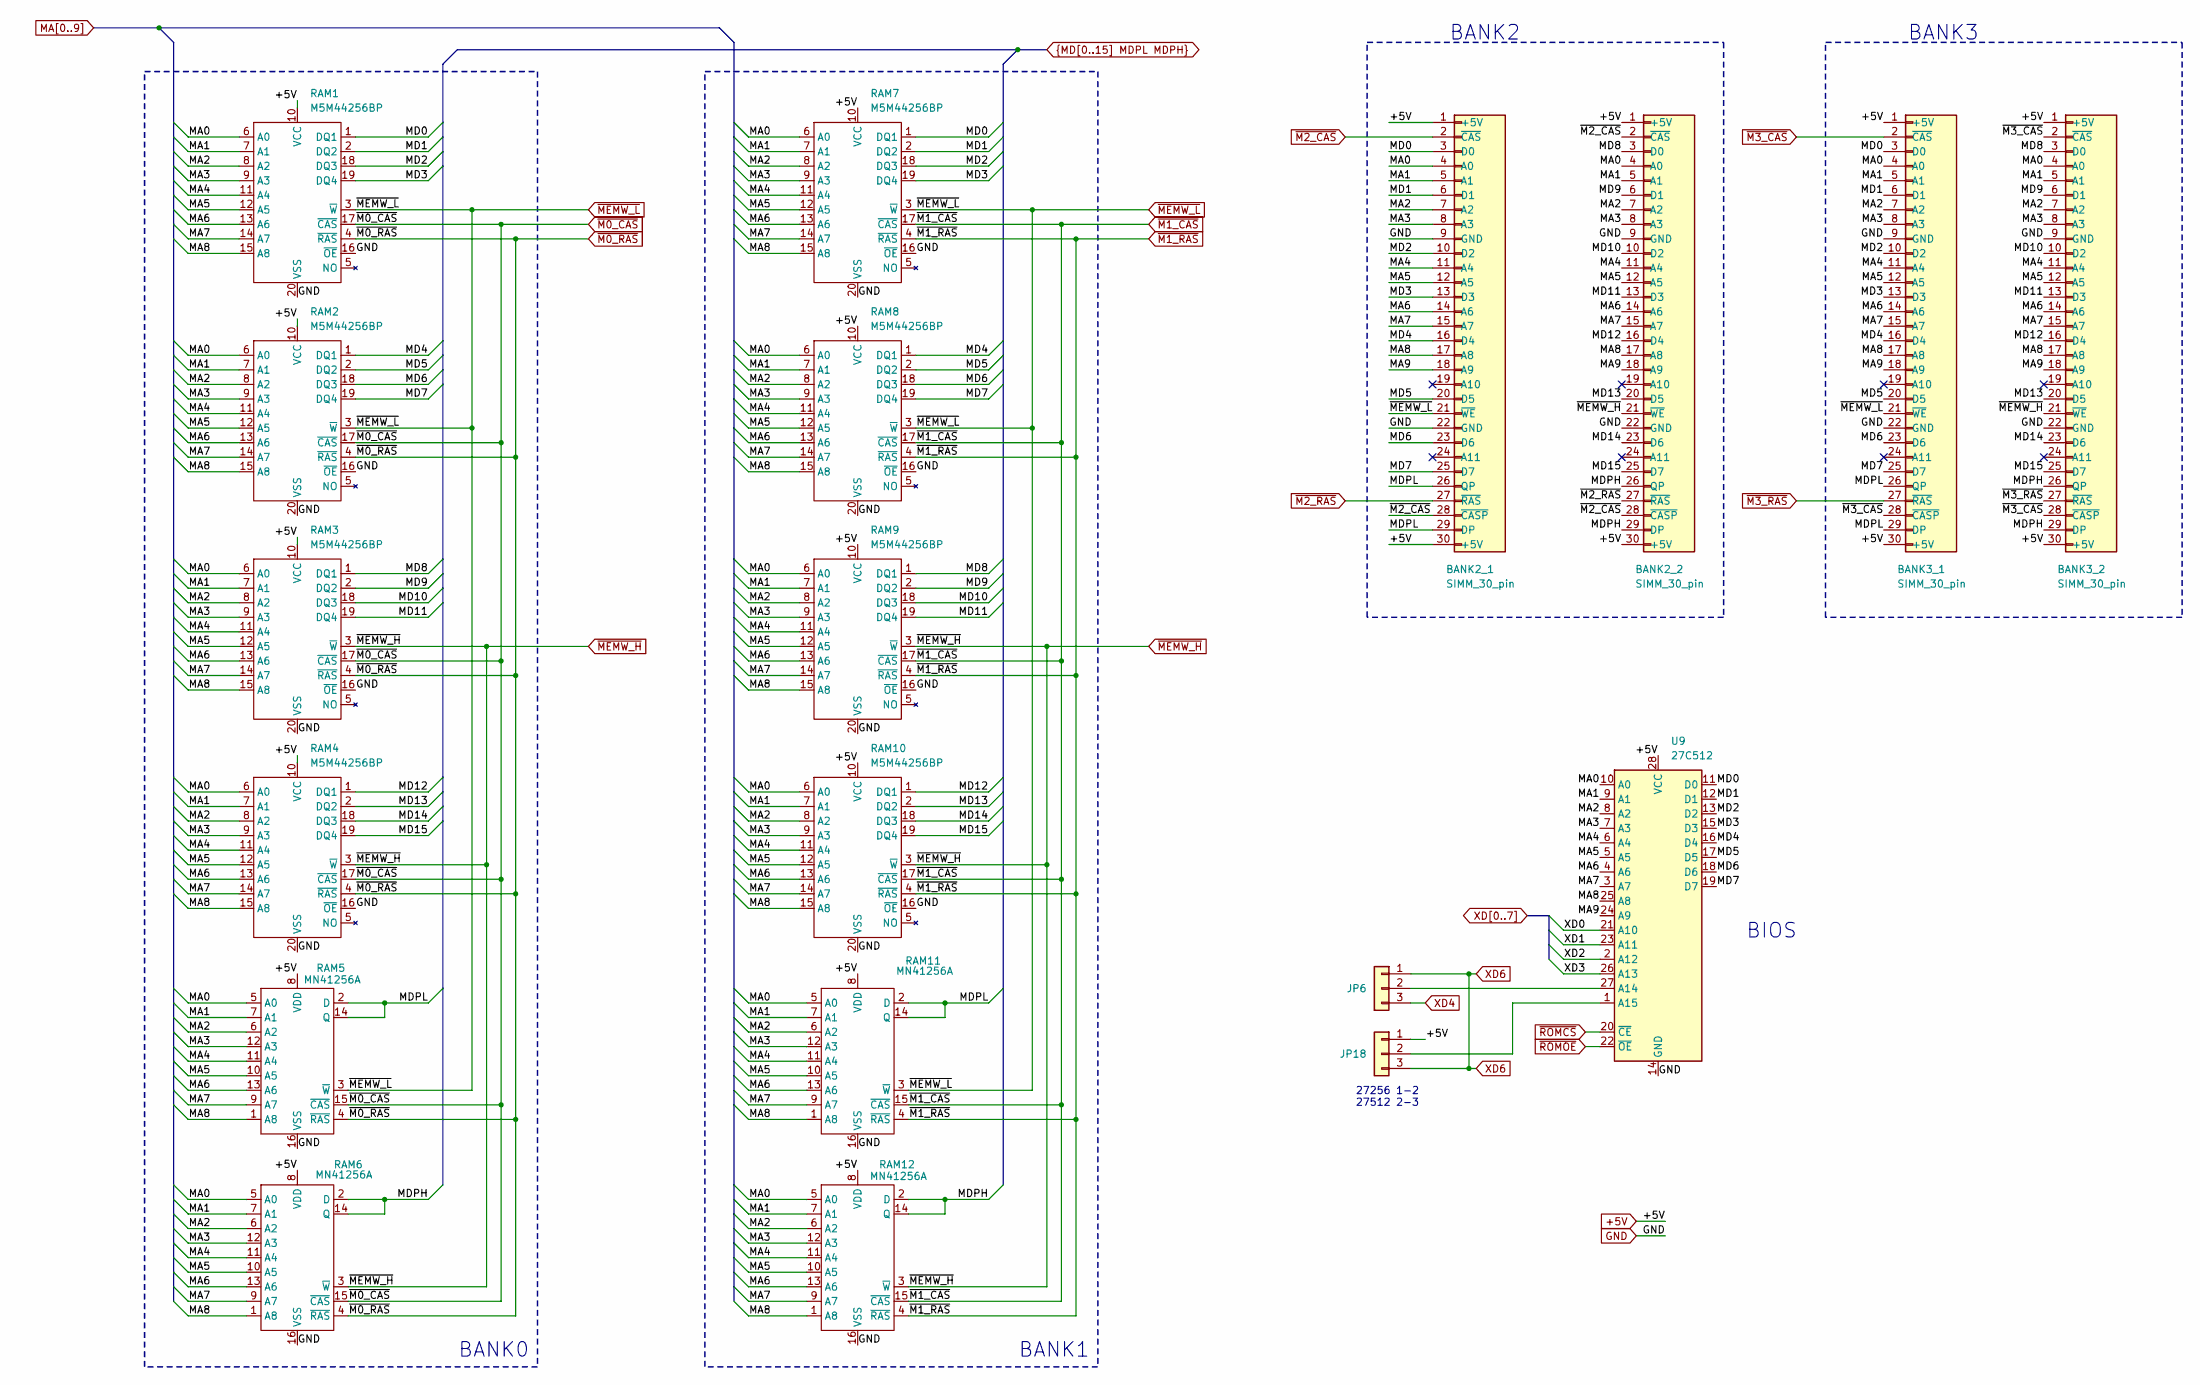
[picture p34: schematic Memory.kicad_sch]

Parts:
BANK2_1, BANK2_2, BANK3_1, BANK3_2: SIMM_30_pin; PinHeader_1x30_P2.54mm_Vertical
JP6, JP18: Conn_01x03; PinHeader_1x03_P2.54mm_Vertical
RAM1, RAM2, RAM3, RAM4, RAM7, RAM8, RAM9, RAM10: M5M44256BP; CERDIP-20_W7.62mm_SideBrazed
RAM5, RAM6, RAM11, RAM12: MN41256A; CERDIP-16_W7.62mm_SideBrazed
U9: 27C512; DIP-28_W15.24mm

Connections:
+5V: BANK2_1.1 (+5V), BANK2_1.30 (+5V), BANK2_2.1 (+5V), BANK2_2.30 (+5V), BANK3_1.1 (+5V), BANK3_1.30 (+5V), BANK3_2.1 (+5V), BANK3_2.30 (+5V), JP18.1, RAM1.10 (VCC), RAM2.10 (VCC), RAM3.10 (VCC), RAM4.10 (VCC), RAM5.8 (VDD), RAM6.8 (VDD), RAM7.10 (VCC), RAM8.10 (VCC), RAM9.10 (VCC), RAM10.10 (VCC), RAM11.8 (VDD), RAM12.8 (VDD), U9.28 (VCC)
GND: BANK2_1.9 (GND), BANK2_1.22 (GND), BANK2_2.9 (GND), BANK2_2.22 (GND), BANK3_1.9 (GND), BANK3_1.22 (GND), BANK3_2.9 (GND), BANK3_2.22 (GND), RAM1.16 (~OE), RAM1.20 (VSS), RAM2.16 (~OE), RAM2.20 (VSS), RAM3.16 (~OE), RAM3.20 (VSS), RAM4.16 (~OE), RAM4.20 (VSS), RAM5.16 (VSS), RAM6.16 (VSS), RAM7.16 (~OE), RAM7.20 (VSS), RAM8.16 (~OE), RAM8.20 (VSS), RAM9.16 (~OE), RAM9.20 (VSS), RAM10.16 (~OE), RAM10.20 (VSS), RAM11.16 (VSS), RAM12.16 (VSS), U9.14 (GND)
MA0: BANK2_1.4 (A0), BANK2_2.4 (A0), BANK3_1.4 (A0), BANK3_2.4 (A0), RAM1.6 (A0), RAM2.6 (A0), RAM3.6 (A0), RAM4.6 (A0), RAM5.5 (A0), RAM6.5 (A0), RAM7.6 (A0), RAM8.6 (A0), RAM9.6 (A0), RAM10.6 (A0), RAM11.5 (A0), RAM12.5 (A0), U9.10 (A0)
MA1: BANK2_1.5 (A1), BANK2_2.5 (A1), BANK3_1.5 (A1), BANK3_2.5 (A1), RAM1.7 (A1), RAM2.7 (A1), RAM3.7 (A1), RAM4.7 (A1), RAM5.7 (A1), RAM6.7 (A1), RAM7.7 (A1), RAM8.7 (A1), RAM9.7 (A1), RAM10.7 (A1), RAM11.7 (A1), RAM12.7 (A1), U9.9 (A1)
MA2: BANK2_1.7 (A2), BANK2_2.7 (A2), BANK3_1.7 (A2), BANK3_2.7 (A2), RAM1.8 (A2), RAM2.8 (A2), RAM3.8 (A2), RAM4.8 (A2), RAM5.6 (A2), RAM6.6 (A2), RAM7.8 (A2), RAM8.8 (A2), RAM9.8 (A2), RAM10.8 (A2), RAM11.6 (A2), RAM12.6 (A2), U9.8 (A2)
MA3: BANK2_1.8 (A3), BANK2_2.8 (A3), BANK3_1.8 (A3), BANK3_2.8 (A3), RAM1.9 (A3), RAM2.9 (A3), RAM3.9 (A3), RAM4.9 (A3), RAM5.12 (A3), RAM6.12 (A3), RAM7.9 (A3), RAM8.9 (A3), RAM9.9 (A3), RAM10.9 (A3), RAM11.12 (A3), RAM12.12 (A3), U9.7 (A3)
MA4: BANK2_1.11 (A4), BANK2_2.11 (A4), BANK3_1.11 (A4), BANK3_2.11 (A4), RAM1.11 (A4), RAM2.11 (A4), RAM3.11 (A4), RAM4.11 (A4), RAM5.11 (A4), RAM6.11 (A4), RAM7.11 (A4), RAM8.11 (A4), RAM9.11 (A4), RAM10.11 (A4), RAM11.11 (A4), RAM12.11 (A4), U9.6 (A4)
MA5: BANK2_1.12 (A5), BANK2_2.12 (A5), BANK3_1.12 (A5), BANK3_2.12 (A5), RAM1.12 (A5), RAM2.12 (A5), RAM3.12 (A5), RAM4.12 (A5), RAM5.10 (A5), RAM6.10 (A5), RAM7.12 (A5), RAM8.12 (A5), RAM9.12 (A5), RAM10.12 (A5), RAM11.10 (A5), RAM12.10 (A5), U9.5 (A5)
MA6: BANK2_1.14 (A6), BANK2_2.14 (A6), BANK3_1.14 (A6), BANK3_2.14 (A6), RAM1.13 (A6), RAM2.13 (A6), RAM3.13 (A6), RAM4.13 (A6), RAM5.13 (A6), RAM6.13 (A6), RAM7.13 (A6), RAM8.13 (A6), RAM9.13 (A6), RAM10.13 (A6), RAM11.13 (A6), RAM12.13 (A6), U9.4 (A6)
MA7: BANK2_1.15 (A7), BANK2_2.15 (A7), BANK3_1.15 (A7), BANK3_2.15 (A7), RAM1.14 (A7), RAM2.14 (A7), RAM3.14 (A7), RAM4.14 (A7), RAM5.9 (A7), RAM6.9 (A7), RAM7.14 (A7), RAM8.14 (A7), RAM9.14 (A7), RAM10.14 (A7), RAM11.9 (A7), RAM12.9 (A7), U9.3 (A7)
MA8: BANK2_1.17 (A8), BANK2_2.17 (A8), BANK3_1.17 (A8), BANK3_2.17 (A8), RAM1.15 (A8), RAM2.15 (A8), RAM3.15 (A8), RAM4.15 (A8), RAM5.1 (A8), RAM6.1 (A8), RAM7.15 (A8), RAM8.15 (A8), RAM9.15 (A8), RAM10.15 (A8), RAM11.1 (A8), RAM12.1 (A8), U9.25 (A8)
MA9: BANK2_1.18 (A9), BANK2_2.18 (A9), BANK3_1.18 (A9), BANK3_2.18 (A9), U9.24 (A9)
MD0: BANK2_1.3 (D0), BANK3_1.3 (D0), RAM1.1 (DQ1), RAM7.1 (DQ1), U9.11 (D0)
MD1: BANK2_1.6 (D1), BANK3_1.6 (D1), RAM1.2 (DQ2), RAM7.2 (DQ2), U9.12 (D1)
MD2: BANK2_1.10 (D2), BANK3_1.10 (D2), RAM1.18 (DQ3), RAM7.18 (DQ3), U9.13 (D2)
MD3: BANK2_1.13 (D3), BANK3_1.13 (D3), RAM1.19 (DQ4), RAM7.19 (DQ4), U9.15 (D3)
MD4: BANK2_1.16 (D4), BANK3_1.16 (D4), RAM2.1 (DQ1), RAM8.1 (DQ1), U9.16 (D4)
MD5: BANK2_1.20 (D5), BANK3_1.20 (D5), RAM2.2 (DQ2), RAM8.2 (DQ2), U9.17 (D5)
MD6: BANK2_1.23 (D6), BANK3_1.23 (D6), RAM2.18 (DQ3), RAM8.18 (DQ3), U9.18 (D6)
MD7: BANK2_1.25 (D7), BANK3_1.25 (D7), RAM2.19 (DQ4), RAM8.19 (DQ4), U9.19 (D7)
MD8: BANK2_2.3 (D0), BANK3_2.3 (D0), RAM3.1 (DQ1), RAM9.1 (DQ1)
MD9: BANK2_2.6 (D1), BANK3_2.6 (D1), RAM3.2 (DQ2), RAM9.2 (DQ2)
MD10: BANK2_2.10 (D2), BANK3_2.10 (D2), RAM3.18 (DQ3), RAM9.18 (DQ3)
MD11: BANK2_2.13 (D3), BANK3_2.13 (D3), RAM3.19 (DQ4), RAM9.19 (DQ4)
MD12: BANK2_2.16 (D4), BANK3_2.16 (D4), RAM4.1 (DQ1), RAM10.1 (DQ1)
MD13: BANK2_2.20 (D5), BANK3_2.20 (D5), RAM4.2 (DQ2), RAM10.2 (DQ2)
MD14: BANK2_2.23 (D6), BANK3_2.23 (D6), RAM4.18 (DQ3), RAM10.18 (DQ3)
MD15: BANK2_2.25 (D7), BANK3_2.25 (D7), RAM4.19 (DQ4), RAM10.19 (DQ4)
MDPH: BANK2_2.26 (QP), BANK2_2.29 (DP), BANK3_2.26 (QP), BANK3_2.29 (DP), RAM6.2 (D), RAM6.14 (Q), RAM12.2 (D), RAM12.14 (Q)
MDPL: BANK2_1.26 (QP), BANK2_1.29 (DP), BANK3_1.26 (QP), BANK3_1.29 (DP), RAM5.2 (D), RAM5.14 (Q), RAM11.2 (D), RAM11.14 (Q)
unnamed: JP6.2, U9.27 (A14)
unnamed: JP18.2, U9.1 (A15)
XD0: U9.21 (A10)
XD1: U9.23 (A11)
XD2: U9.2 (A12)
XD3: U9.26 (A13)
XD4: JP6.3
XD6: JP6.1, JP18.3
~M0_CAS: RAM1.17 (~CAS), RAM2.17 (~CAS), RAM3.17 (~CAS), RAM4.17 (~CAS), RAM5.15 (~CAS), RAM6.15 (~CAS)
~M0_RAS: RAM1.4 (~RAS), RAM2.4 (~RAS), RAM3.4 (~RAS), RAM4.4 (~RAS), RAM5.4 (~RAS), RAM6.4 (~RAS)
~M1_CAS: RAM7.17 (~CAS), RAM8.17 (~CAS), RAM9.17 (~CAS), RAM10.17 (~CAS), RAM11.15 (~CAS), RAM12.15 (~CAS)
~M1_RAS: RAM7.4 (~RAS), RAM8.4 (~RAS), RAM9.4 (~RAS), RAM10.4 (~RAS), RAM11.4 (~RAS), RAM12.4 (~RAS)
~M2_CAS: BANK2_1.2 (~CAS), BANK2_1.28 (~CASP), BANK2_2.2 (~CAS), BANK2_2.28 (~CASP)
~M2_RAS: BANK2_1.27 (~RAS), BANK2_2.27 (~RAS)
~M3_CAS: BANK3_1.2 (~CAS), BANK3_1.28 (~CASP), BANK3_2.2 (~CAS), BANK3_2.28 (~CASP)
~M3_RAS: BANK3_1.27 (~RAS), BANK3_2.27 (~RAS)
~MEMW_H: BANK2_2.21 (~WE), BANK3_2.21 (~WE), RAM3.3 (~W), RAM4.3 (~W), RAM6.3 (~W), RAM9.3 (~W), RAM10.3 (~W), RAM12.3 (~W)
~MEMW_L: BANK2_1.21 (~WE), BANK3_1.21 (~WE), RAM1.3 (~W), RAM2.3 (~W), RAM5.3 (~W), RAM7.3 (~W), RAM8.3 (~W), RAM11.3 (~W)
~ROMCS: U9.20 (~CE)
~ROMOE: U9.22 (~OE)

Notes on the sheet:
BANK0
BANK1
BANK3
BANK2
BIOS
27256 1-2 27512 2-3
