TomasPavlovicPavlo/286_schematic/IDE_controller/IMG_6856.JPG

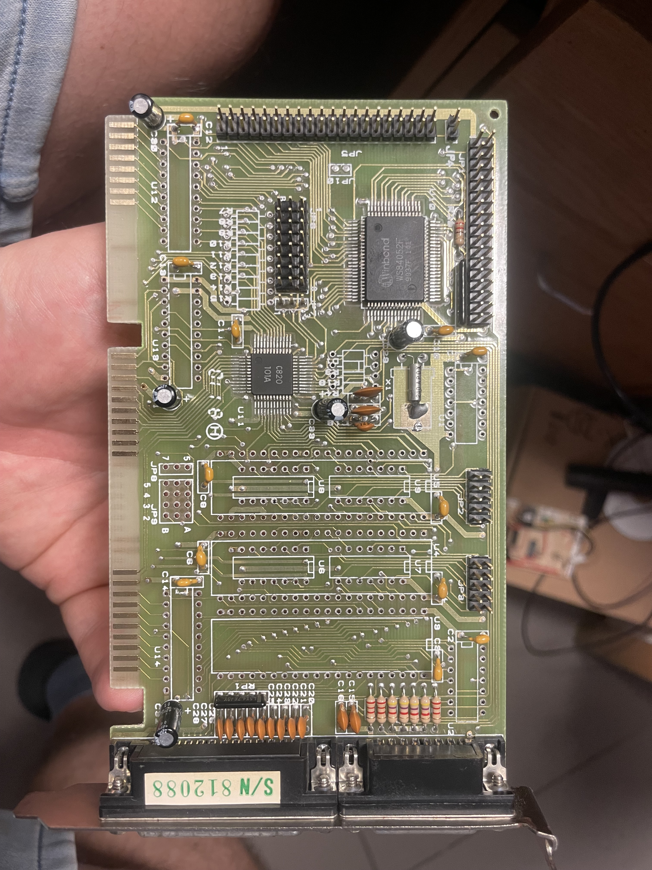
IDE_controller/IMG_6856.JPG
