TomasPavlovicPavlo/286_schematic/KiCAD/IMG_6815.JPG

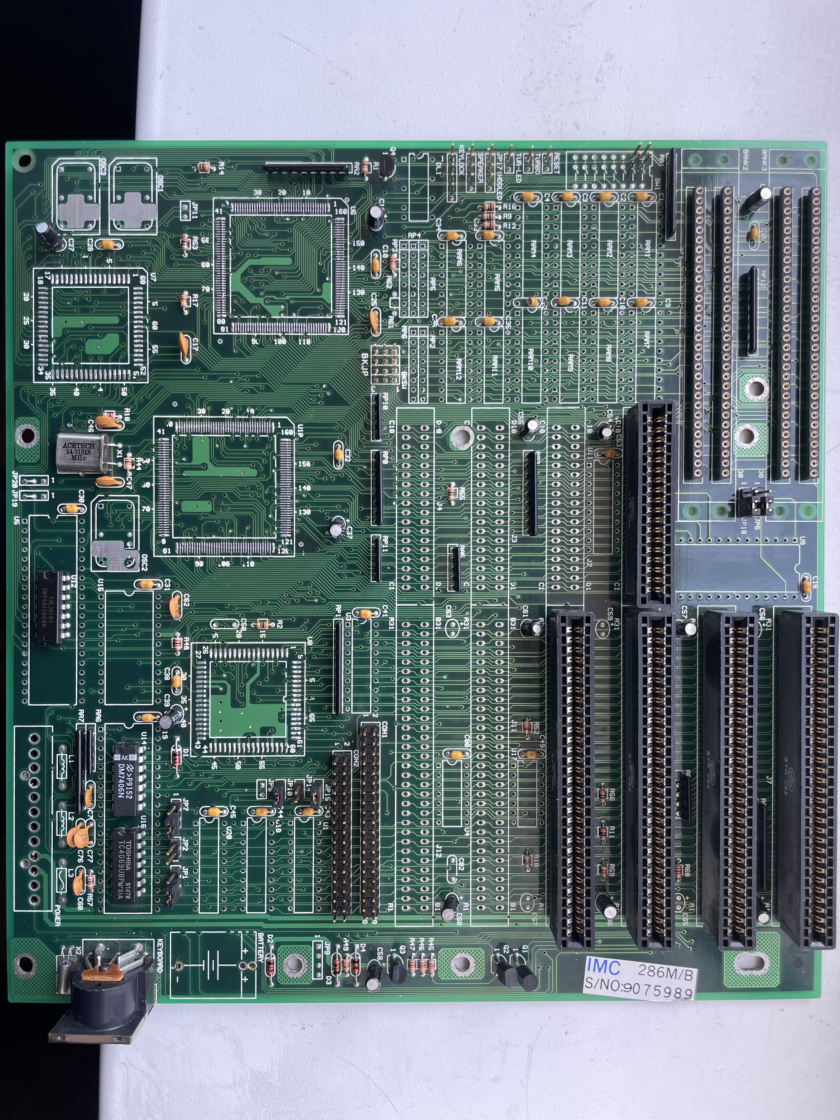
KiCAD/IMG_6815.JPG
